berlinkeys/Berlin/EDA/ressources/acheron_3d_models/BM04B-ASRS-TF.STEP

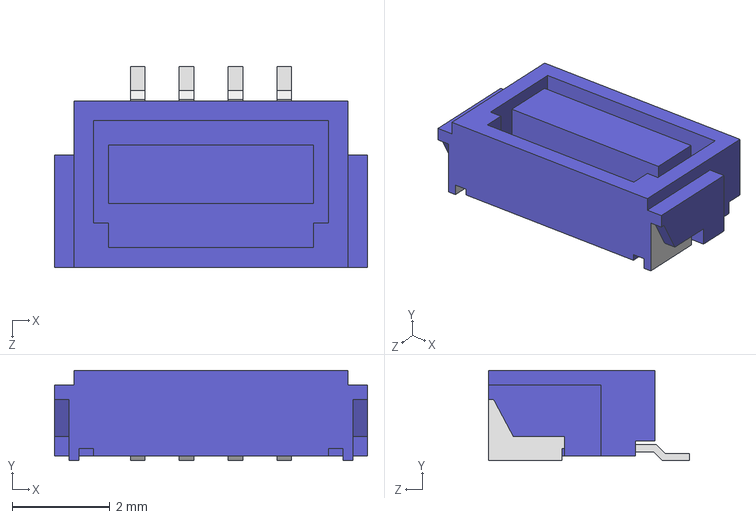
[picture p15: CAD file, 2022-06-08]
EDA/ressources/acheron_3d_models/BM04B-ASRS-TF.STEP
6.40 x 1.85 x 4.10 mm
