berlinkeys/Berlin/EDA/ressources/acheron_3d_models/XM7D-0512.STEP

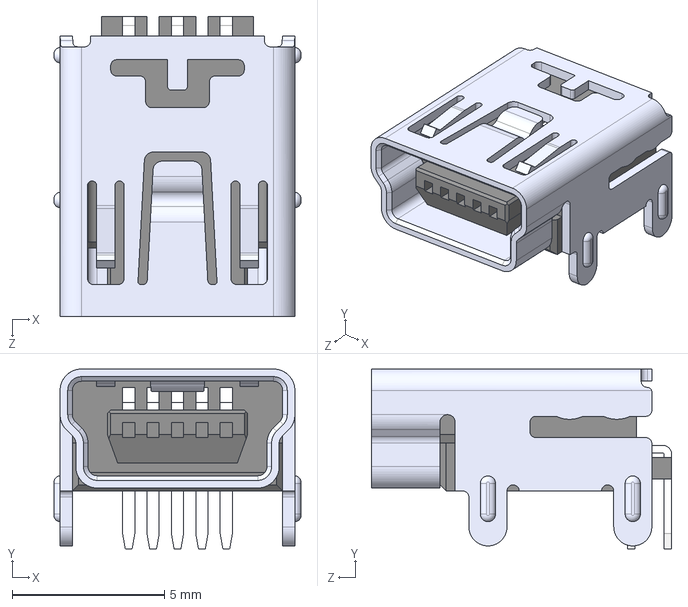
[picture p16: CAD file, 2022-06-08]
EDA/ressources/acheron_3d_models/XM7D-0512.STEP
8.10 x 5.90 x 9.85 mm
