berlinkeys/Berlin/EDA/ressources/acheron_3d_models/MDBT40.step

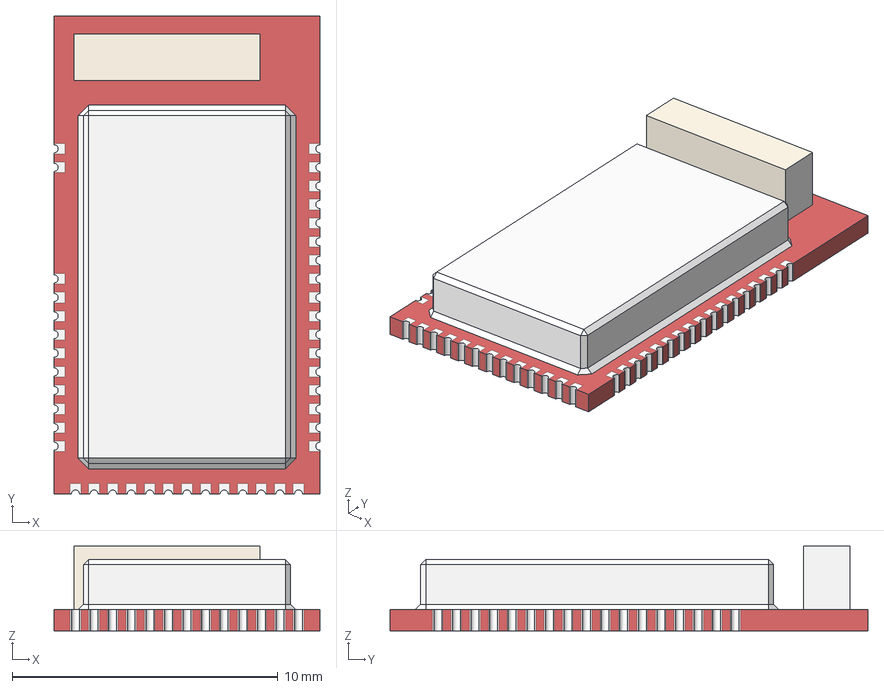
[picture p17: CAD file, 2022-06-08]
EDA/ressources/acheron_3d_models/MDBT40.step
10.0 x 18.0 x 3.20 mm
