berlinkeys/Berlin/EDA/ressources/acheron_3d_models/5032_XTAL.step

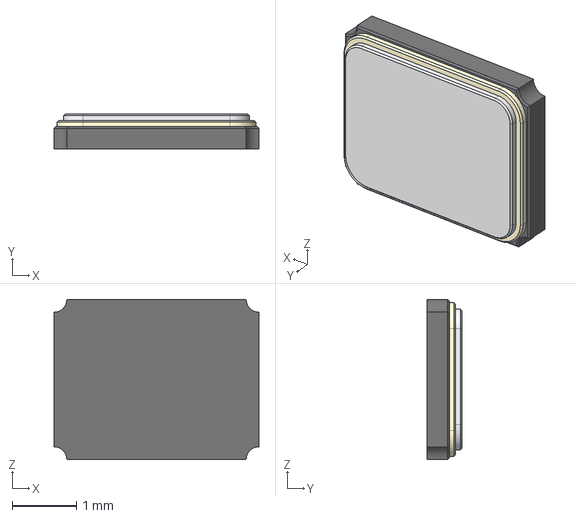
[picture p18: CAD file, 2022-06-08]
EDA/ressources/acheron_3d_models/5032_XTAL.step
3.20 x 0.55 x 2.50 mm
