berlinkeys/Berlin/EDA/ressources/acheron_3d_models/6028SMDRGB.iges

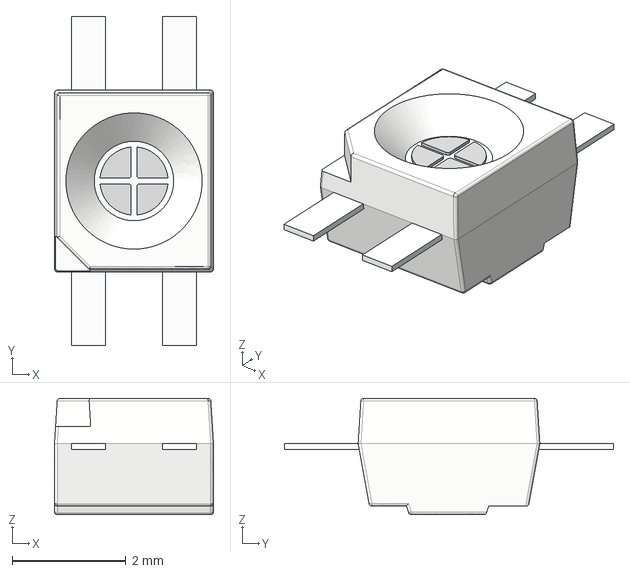
[picture p19: CAD file, 2022-06-08]
EDA/ressources/acheron_3d_models/6028SMDRGB.iges
2.80 x 5.80 x 2.05 mm
