berlinkeys/Berlin/EDA/ressources/acheron_3d_models/angle4PinHeader.step

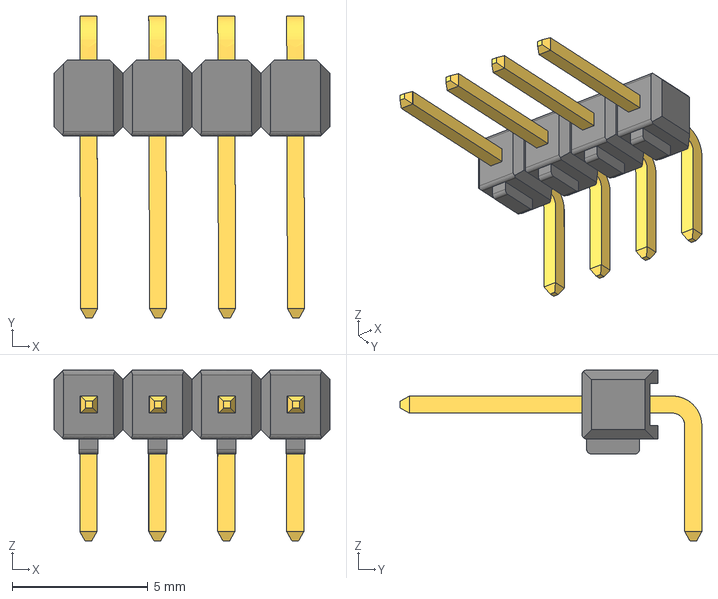
[picture p20: CAD file, 2022-06-08]
EDA/ressources/acheron_3d_models/angle4PinHeader.step
10.2 x 11.1 x 6.29 mm
