berlinkeys/Berlin/EDA/ressources/acheron_3d_models/E6C1209RGB.iges

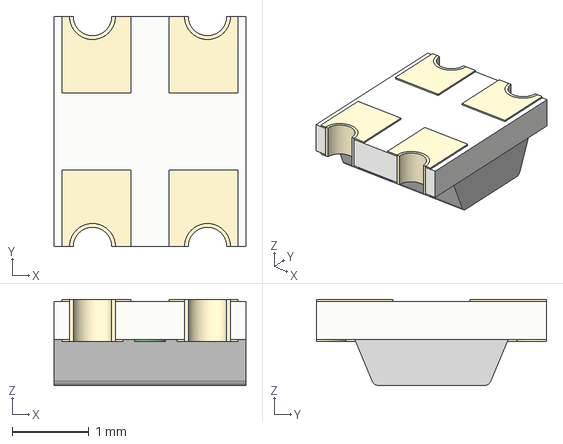
[picture p21: CAD file, 2022-06-08]
EDA/ressources/acheron_3d_models/E6C1209RGB.iges
2.50 x 3.00 x 1.12 mm
