berlinkeys/Berlin/EDA/ressources/acheron_3d_models/TE-2132415-4.stp

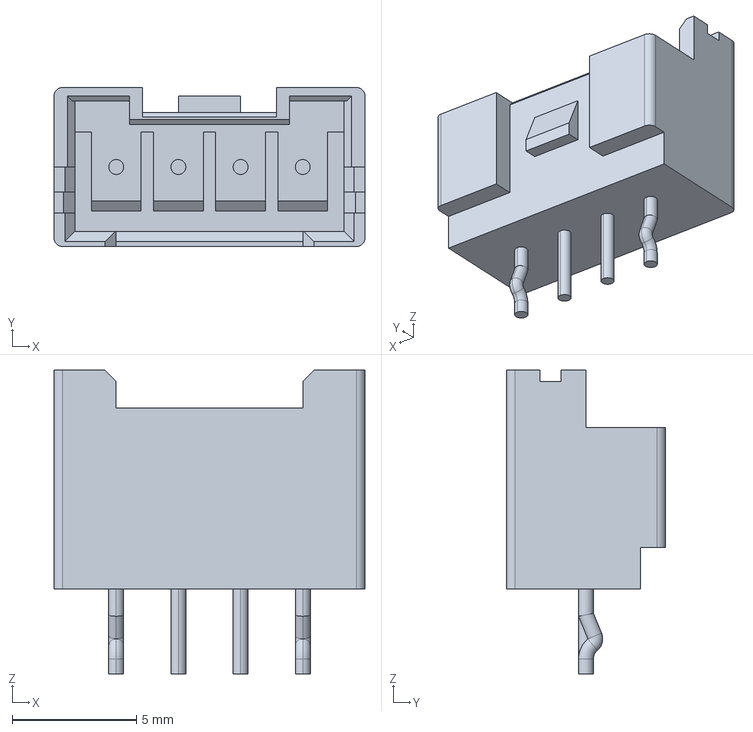
[picture p22: CAD file, 2022-06-08]
EDA/ressources/acheron_3d_models/TE-2132415-4.stp
12.5 x 6.40 x 12.2 mm
