berlinkeys/Berlin/EDA/ressources/acheron_3d_models/WS2812.stp

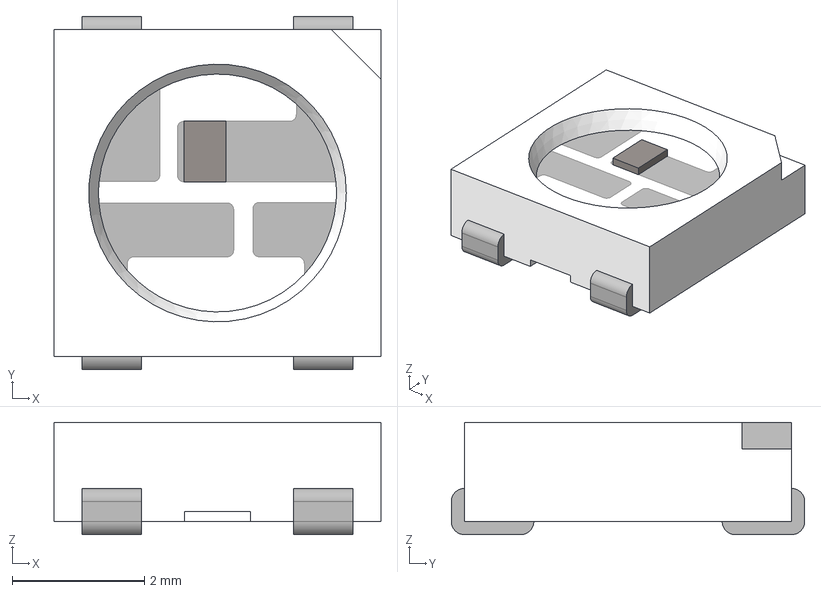
[picture p23: CAD file, 2022-06-08]
EDA/ressources/acheron_3d_models/WS2812.stp
4.95 x 5.35 x 1.70 mm
