berlinkeys/Berlin/EDA/ressources/acheron_3d_models/ALPS_EC11E.stp

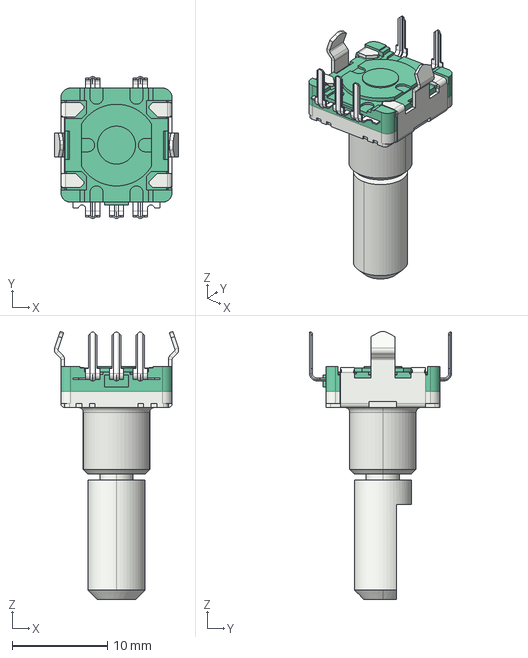
[picture p24: CAD file, 2022-06-08]
EDA/ressources/acheron_3d_models/ALPS_EC11E.stp
13.1 x 15.0 x 28.2 mm
