berlinkeys/Berlin/EDA/ressources/acheron_3d_models/BM04B-SRSS.step

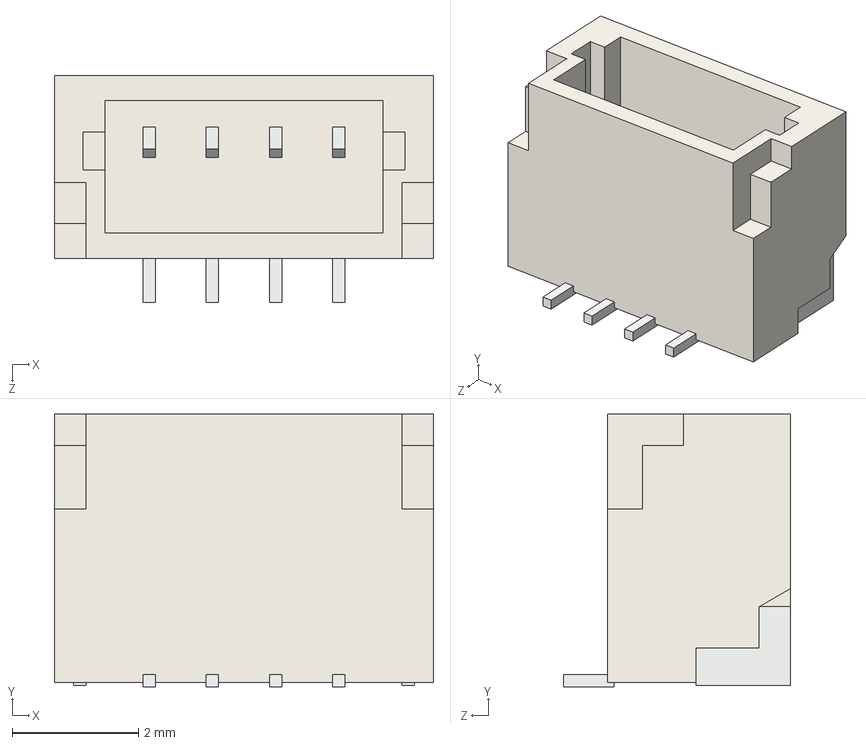
[picture p25: CAD file, 2022-06-08]
EDA/ressources/acheron_3d_models/BM04B-SRSS.step
6.00 x 4.32 x 3.60 mm
