berlinkeys/Berlin/EDA/ressources/acheron_3d_models/TYPE-C-31-M-12.step

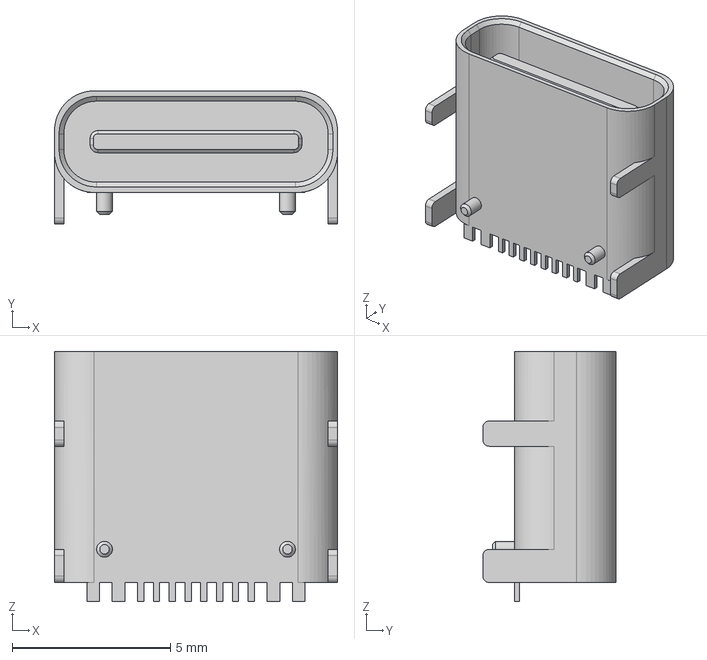
[picture p26: CAD file, 2022-06-08]
EDA/ressources/acheron_3d_models/TYPE-C-31-M-12.step
8.94 x 4.21 x 7.90 mm
