berlinkeys/Berlin/EDA/ressources/acheron_3d_models/ACM2012-2P.STEP

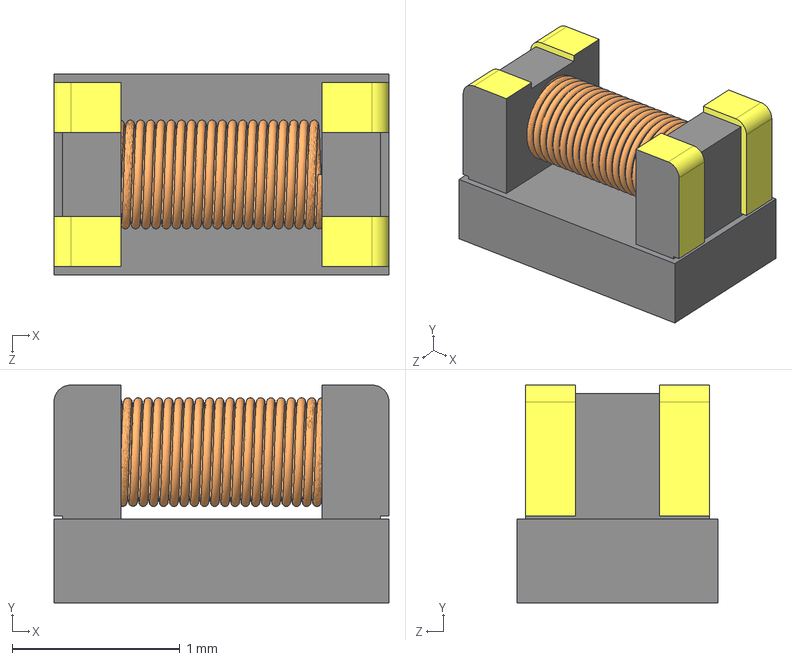
[picture p27: CAD file, 2022-06-08]
EDA/ressources/acheron_3d_models/ACM2012-2P.STEP
2.00 x 1.30 x 1.20 mm
