berlinkeys/Berlin/EDA/ressources/acheron_3d_models/RKJXT1F42001.step

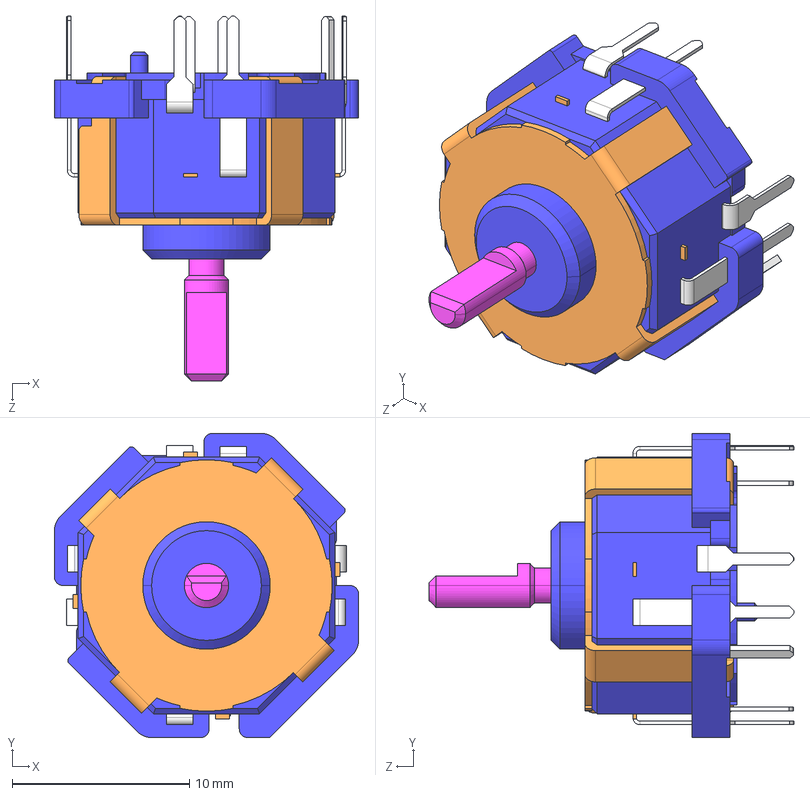
[picture p28: CAD file, 2022-06-08]
EDA/ressources/acheron_3d_models/RKJXT1F42001.step
17.2 x 17.2 x 20.6 mm
