berlinkeys/Berlin/EDA/ressources/acheron_3d_models/UX60SC-MB-5S8.stp

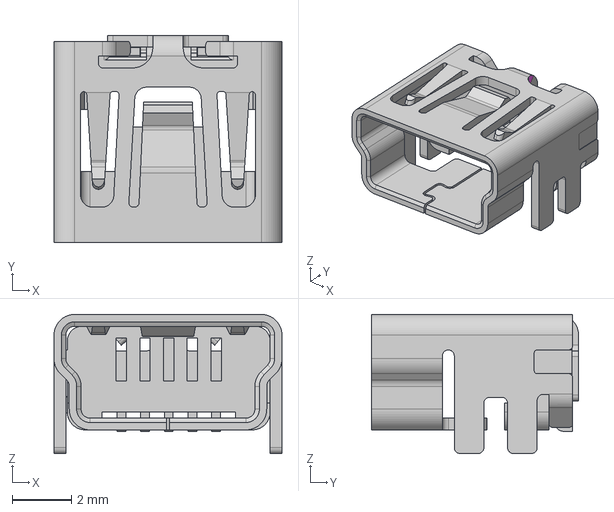
[picture p29: CAD file, 2022-06-08]
EDA/ressources/acheron_3d_models/UX60SC-MB-5S8.stp
7.70 x 7.00 x 4.70 mm
