berlinkeys/Berlin/EDA/ressources/acheron_3d_models/TYPE-C-31-M-14.step

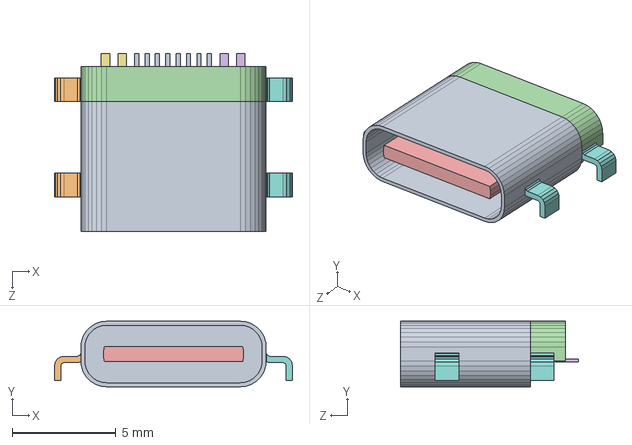
[picture p30: CAD file, 2022-06-08]
EDA/ressources/acheron_3d_models/TYPE-C-31-M-14.step
11.5 x 3.16 x 8.58 mm
