berlinkeys/Berlin/EDA/ressources/acheron_3d_models/keystone-PN3030TR.STEP

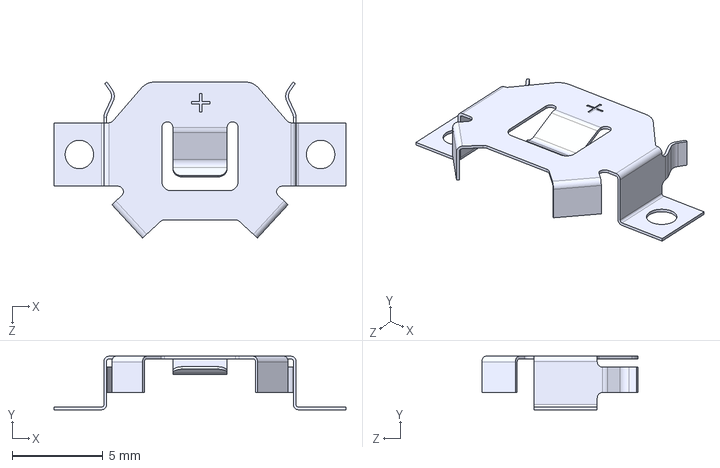
[picture p32: CAD file, 2022-06-08]
EDA/ressources/acheron_3d_models/keystone-PN3030TR.STEP
16.1 x 2.95 x 8.61 mm
