berlinkeys/Berlin/EDA/ressources/acheron_3d_models/male6PinHeader.stp

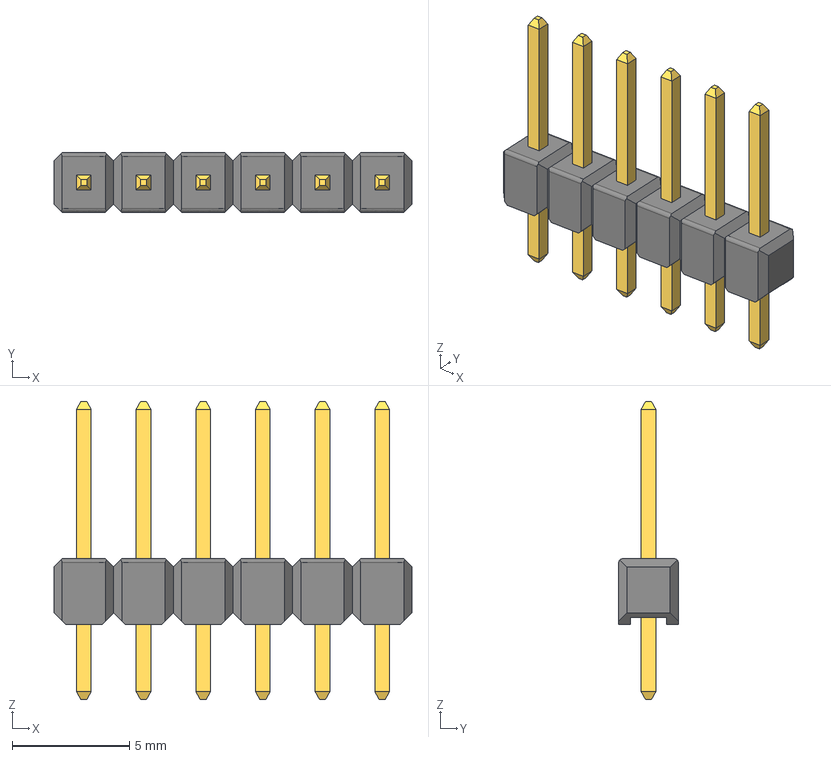
[picture p33: CAD file, 2022-06-08]
EDA/ressources/acheron_3d_models/male6PinHeader.stp
15.2 x 2.54 x 12.7 mm
