berlinkeys/Berlin/EDA/ressources/acheron_3d_models/SM20B-SRSS-TB.STEP

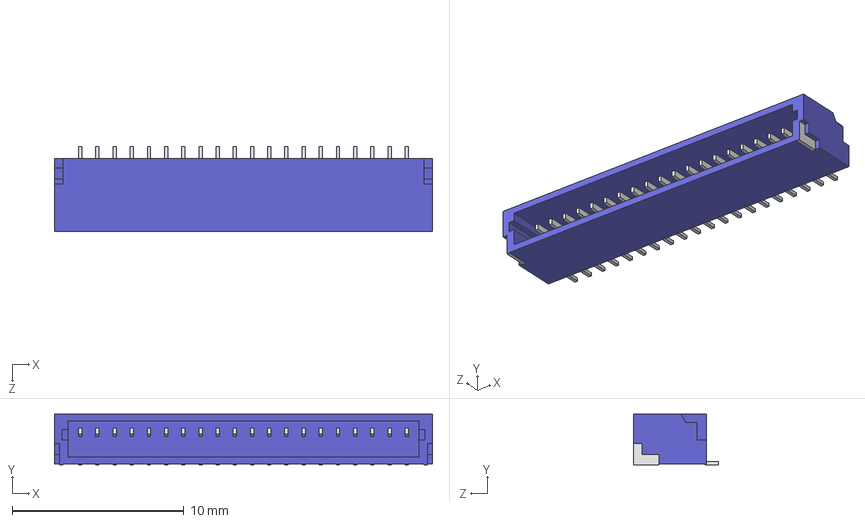
[picture p34: CAD file, 2022-06-08]
EDA/ressources/acheron_3d_models/SM20B-SRSS-TB.STEP
22.0 x 2.96 x 4.95 mm
