berlinkeys/Berlin/EDA/ressources/acheron_3d_models/Tactile_SMD_PushBtn_5x5mm.STEP

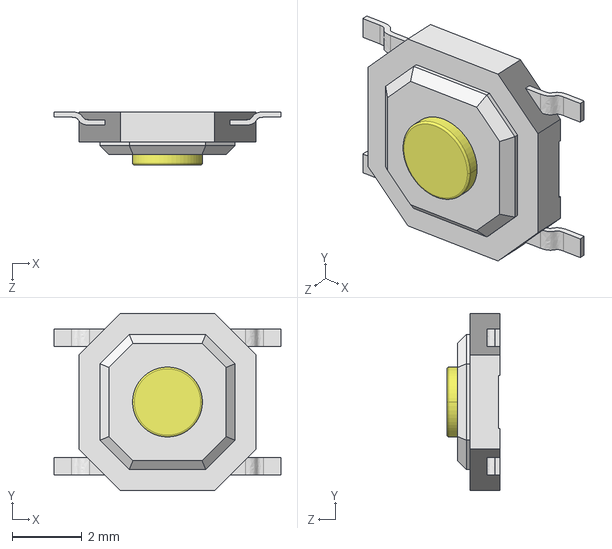
[picture p35: CAD file, 2022-06-08]
EDA/ressources/acheron_3d_models/Tactile_SMD_PushBtn_5x5mm.STEP
6.50 x 5.08 x 1.52 mm
