berlinkeys/Berlin/EDA/ressources/acheron_3d_models/kailh_socket_mx.stp

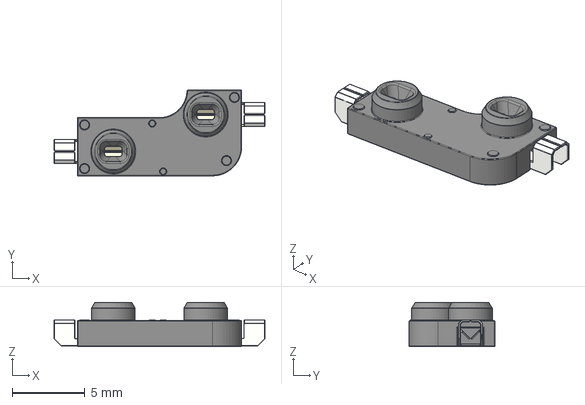
[picture p36: CAD file, 2022-06-08]
EDA/ressources/acheron_3d_models/kailh_socket_mx.stp
14.5 x 5.89 x 3.05 mm
