berlinkeys/Berlin/EDA/ressources/acheron_3d_models/SM04B-SRSS-TB.STEP

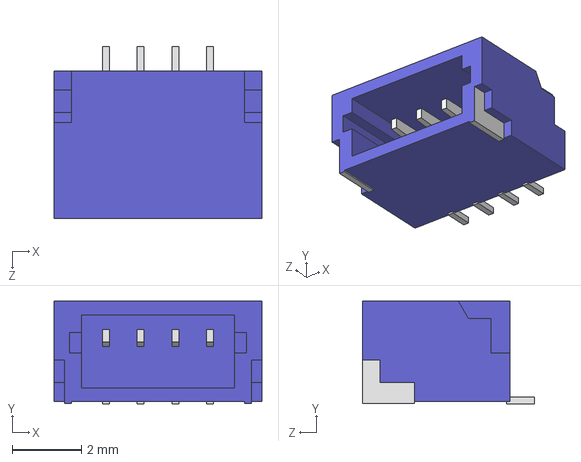
[picture p37: CAD file, 2022-06-08]
EDA/ressources/acheron_3d_models/SM04B-SRSS-TB.STEP
6.00 x 2.96 x 4.95 mm
