berlinkeys/Berlin/EDA/ressources/acheron_3d_models/3313J-1-202E.stp

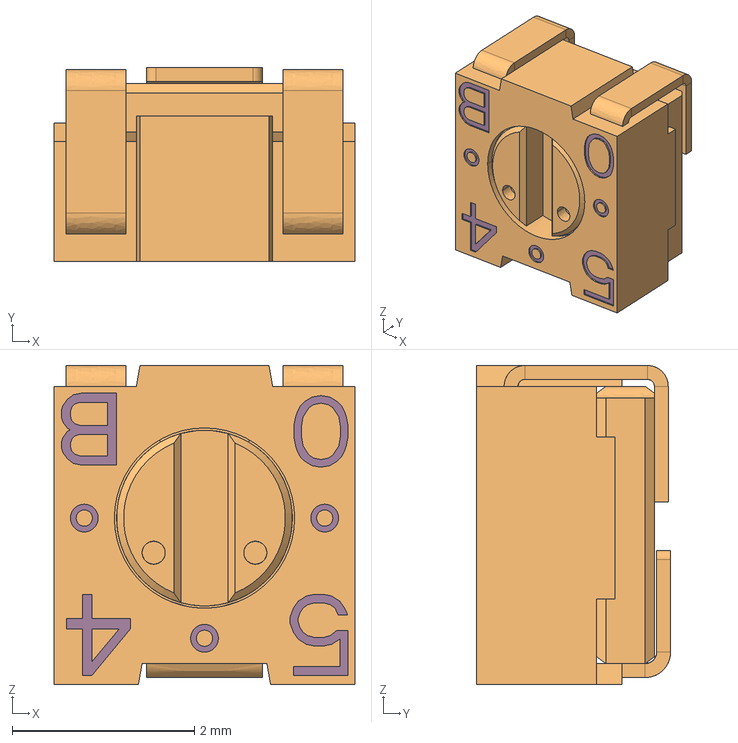
[picture p38: CAD file, 2022-06-08]
EDA/ressources/acheron_3d_models/3313J-1-202E.stp
3.30 x 2.13 x 3.51 mm
