berlinkeys/Berlin/EDA/ressources/acheron_3d_models/4PinHeader.step

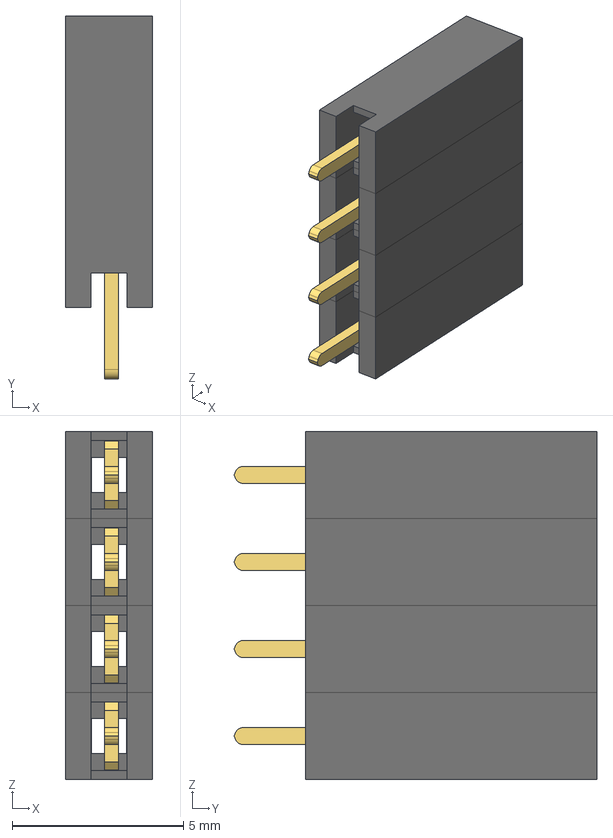
[picture p39: CAD file, 2022-06-08]
EDA/ressources/acheron_3d_models/4PinHeader.step
2.54 x 10.6 x 10.2 mm
header-1 x 4
pin-1 x 4
