berlinkeys/Berlin/EDA/ressources/acheron_3d_models/mx_switch.step

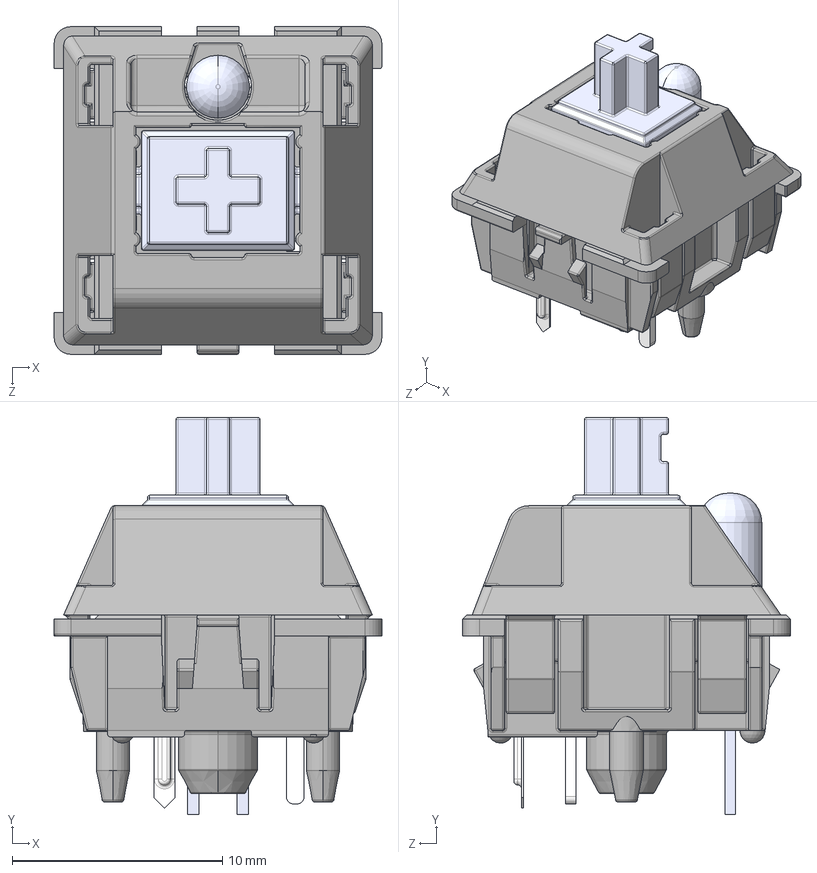
[picture p40: CAD file, 2022-06-08]
EDA/ressources/acheron_3d_models/mx_switch.step
15.6 x 18.9 x 15.6 mm
MX 轴 按键′_ü___¨1
MX 轴 轴体áì_¨￠¨__
MX粣 拸簽LEDLEDLED
MX轴 轴体 底部 μ×2__默认_á2____è_
针脚___默认__è_
