berlinkeys/Berlin/EDA/snapshot_0.7/berlin.kicad_sch

## KiCad design EDA/snapshot_0.7/berlin.kicad_sch (2023-06-23, an earlier design)

Schematic: berlin.kicad_sch

Parts:
C101, C102: 100n; C_1206_3216Metric_Pad1.42x1.75mm_HandSolder
C701, C704, C705, C717: 22uF; C_1206_3216Metric_Pad1.42x1.75mm_HandSolder
C703, C707, C708, C709, C710: 100n; C_0805_2012Metric_Pad1.15x1.40mm_HandSolder
C706, C715: 10u; C_1206_3216Metric_Pad1.42x1.75mm_HandSolder
C711: 100nF; C_0805_2012Metric_Pad1.15x1.40mm_HandSolder
C714: 4.7n; C_0805_2012Metric_Pad1.15x1.40mm_HandSolder
D2, D3, D4, D5, D6, D7, D8, D9, D10, D11, D12, D13, D14, D15, D16, D17, D18, D19, D20, D21, D22, D23, D24, D25, D26, D27, D28, D29, D30, D31, D32, D33, D34, D35, D36, D37, D38, D39, D40, D41, D42, D43, D44, D45, D46, D47, D48, D49, D50, D51, D52, D53, D54, D55, D56, D57, D58, D59, D60, D61, D62, D63, D64, D65, D66, D67, D68, D69, D70, D71, D72, D73, D74, D75, D76, D77, D78, D79, D80, D81, D82, D83, D84, D85, D86, D87, D88, D89, D90, D91, D92, D93, D94, D95, D96, D97, D98, D99, D100, D101, D103, D104, D105, D106, D107, D108, D109, D110, D111, D112, D113, D114, D115, D116, D117, D118, D119, D120, D121, D122, D123, D124, D703: 1N4148; D_SOD-123
D701: RB060M-60TR; D_SOD-123
F701: 1.5A Polyfuse; Fuse_1812_4532Metric_Pad1.30x3.40mm_HandSolder
J201: TYPE-C-31-M12_13; TYPE-C-31-M-12
J202: Conn_ARM_JTAG_SWD_10; PinSocket_2x05_P2.54mm_Vertical
J203: LCDCON
L1, L2, L702: L_Core_Ferrite; L_0805_2012Metric_Pad1.15x1.40mm_HandSolder
L701: 6.8uH; Sumida0624CDMCC
LED1,1, LED1,16: WS2811S; MSOP8_WDS
LED1,2, LED1,3, LED1,4, LED1,5, LED1,6, LED1,7, LED1,8, LED1,9, LED1,10, LED1,11, LED1,12, LED1,13, LED1,14, LED1,15, LED2,1, LED2,2, LED2,3, LED2,4, LED2,5, LED2,6, LED2,7, LED2,8, LED2,9, LED2,10, LED2,11, LED2,12, LED2,13, LED2,14, LED2,15, LED2,16, LED2,17, LED2,18, LED2,19, LED3,1, LED3,2, LED3,3, LED3,4, LED3,5, LED3,6, LED3,7, LED3,8, LED3,9, LED3,10, LED3,11, LED3,12, LED3,13, LED3,14, LED3,15, LED3,16, LED3,17, LED3,18, LED3,19, LED4,1, LED4,2, LED4,3, LED4,4, LED4,5, LED4,6, LED4,7, LED4,8, LED4,9, LED4,10, LED4,11, LED4,12, LED4,13, LED4,14, LED4,15, LED4,16, LED4,17, LED4,18, LED4,19, LED5,1, LED5,2, LED5,3, LED5,4, LED5,5, LED5,6, LED5,7, LED5,8, LED5,9, LED5,10, LED5,11, LED5,12, LED5,13, LED5,14, LED5,15, LED5,16, LED5,17, LED5,18, LED5,19, LED6,1, LED6,2, LED6,3, LED6,4, LED6,5, LED6,6, LED6,7, LED6,8, LED6,9, LED6,10, LED6,11, LED6,12, LED6,13, LED6,15, LED6,17, LED6,18, LED6,19, LED7,1, LED7,2, LED7,3, LED7,5, LED7,6, LED7,7, LED7,8, LED7,9, LED7,10, LED7,11, LED7,12, LED7,13, LED7,14, LED7,15, LED7,16, LED7,17, LED7,18: SK6812MINI-E; SK6812MINI_3535_6028_3.2x2.8mm_Round; MPN SK812MINI-E
Q701: DTC123J; SOT-23
R101, R102: 33; R_0805_2012Metric_Pad1.15x1.40mm_HandSolder
R701: 100k; R_0805_2012Metric_Pad1.15x1.40mm_HandSolder
R702: 1M 1%; R_0805_2012Metric_Pad1.15x1.40mm_HandSolder
R703: 100 1%; R_0805_2012Metric_Pad1.15x1.40mm_HandSolder
R705, R706: 5.1k; R_0805_2012Metric_Pad1.15x1.40mm_HandSolder
R711: 330k 1%; R_0805_2012Metric_Pad1.15x1.40mm_HandSolder
RV204, RV205, RV206: R_Potentiometer_MountingPin
SW1,1, SW1,16: Rotary_Encoder_Switch_Chassis; ALPS_EC11E
SW1,2, SW1,3, SW1,4, SW1,5, SW1,6, SW1,7, SW1,8, SW1,9, SW1,10, SW1,11, SW1,12, SW1,13, SW1,14, SW1,15, SW2,1, SW2,2, SW2,3, SW2,4, SW2,5, SW2,6, SW2,7, SW2,9, SW2,10, SW2,11, SW2,12, SW2,13, SW2,14, SW2,15, SW2,16, SW2,17, SW3,1, SW3,2, SW3,3, SW3,4, SW3,5, SW3,6, SW3,7, SW3,8, SW3,9, SW3,10, SW3,11, SW3,12, SW3,13, SW3,14, SW3,15, SW3,16, SW3,17, SW3,18, SW3,19, SW4,2, SW4,3, SW4,4, SW4,5, SW4,6, SW4,7, SW4,8, SW4,9, SW4,10, SW4,11, SW4,12, SW4,13, SW4,14, SW4,15, SW4,16, SW4,17, SW4,18, SW4,19, SW5,2, SW5,3, SW5,4, SW5,5, SW5,6, SW5,7, SW5,8, SW5,9, SW5,10, SW5,11, SW5,12, SW5,13, SW5,14, SW5,15, SW5,16, SW5,17, SW5,18, SW5,19, SW6,2, SW6,3, SW6,4, SW6,5, SW6,6, SW6,7, SW6,8, SW6,9, SW6,10, SW6,11, SW6,12, SW6,15, SW6,17, SW6,18, SW6,19, SW7,8, SW7,10, SW7,11, SW7,12, SW7,14, SW7,15, SW7,16, SW7,18: MXSwitch; MX100
SW2,18, SW7,17: MXSwitch; MX200
SW2,19: MXSwitch; MX200R
SW4,1, SW7,9: MXSwitch; MX150
SW5,1, SW6,1, SW7,1, SW7,2, SW7,3: MXSwitch; MX125
SW6,13: MXSwitch; MX_ISOEnter
SW7,6: MXSwitch; MX625
SW7,13: MXSwitch; MX175
SW201: SW_Push; SW_PUSH_6mm_H5mm
U501: STM32F072VBTx; LQFP-100_14x14mm_P0.5mm
U701: USBLC6-2SC6; SOT-23-6
U702: AP63203WU-7; TSOT-23-6_HandSoldering

Connections:
1,1 B: LED1,1.3 (OUTB), SW1,1.4 (B)
1,1 G: LED1,1.2 (OUTG), SW1,1.2 (G)
1,1 INTERRUPT: SW1,1.3 (SW), SW1,16.3 (SW)
1,1 R: LED1,1.1 (OUTR), SW1,1.1 (R)
1,16 B: LED1,16.3 (OUTB), SW1,16.4 (B)
1,16 G: LED1,16.2 (OUTG), SW1,16.2 (G)
1,16 R: LED1,16.1 (OUTR), SW1,16.1 (R)
+3.3V: C704.1, C705.1, C706.1, C707.1, C708.1, C709.1, C710.1, C717.1, J202.1 (VCC), L701.2, SW201.1, U501.6 (VBAT), U501.21 (VDDA), U501.28 (VDD), U501.50 (VDD), U501.75 (VDDIO2), U501.100 (VDD), U702.1 (FB)
+5V: C701.1, D701.1 (K), F701.1, LED1,2.1 (VDD), LED1,3.1 (VDD), LED1,4.1 (VDD), LED1,5.1 (VDD), LED1,6.1 (VDD), LED1,7.1 (VDD), LED1,8.1 (VDD), LED1,9.1 (VDD), LED1,10.1 (VDD), LED1,11.1 (VDD), LED1,12.1 (VDD), LED1,13.1 (VDD), LED1,14.1 (VDD), LED1,15.1 (VDD), LED2,1.1 (VDD), LED2,2.1 (VDD), LED2,3.1 (VDD), LED2,4.1 (VDD), LED2,5.1 (VDD), LED2,6.1 (VDD), LED2,7.1 (VDD), LED2,8.1 (VDD), LED2,9.1 (VDD), LED2,10.1 (VDD), LED2,11.1 (VDD), LED2,12.1 (VDD), LED2,13.1 (VDD), LED2,14.1 (VDD), LED2,15.1 (VDD), LED2,16.1 (VDD), LED2,17.1 (VDD), LED2,18.1 (VDD), LED2,19.1 (VDD), LED3,1.1 (VDD), LED3,2.1 (VDD), LED3,3.1 (VDD), LED3,4.1 (VDD), LED3,5.1 (VDD), LED3,6.1 (VDD), LED3,7.1 (VDD), LED3,8.1 (VDD), LED3,9.1 (VDD), LED3,10.1 (VDD), LED3,11.1 (VDD), LED3,12.1 (VDD), LED3,13.1 (VDD), LED3,14.1 (VDD), LED3,15.1 (VDD), LED3,16.1 (VDD), LED3,17.1 (VDD), LED3,18.1 (VDD), LED3,19.1 (VDD), LED4,1.1 (VDD), LED4,2.1 (VDD), LED4,3.1 (VDD), LED4,4.1 (VDD), LED4,5.1 (VDD), LED4,6.1 (VDD), LED4,7.1 (VDD), LED4,8.1 (VDD), LED4,9.1 (VDD), LED4,10.1 (VDD), LED4,11.1 (VDD), LED4,12.1 (VDD), LED4,13.1 (VDD), LED4,14.1 (VDD), LED4,15.1 (VDD), LED4,16.1 (VDD), LED4,17.1 (VDD), LED4,18.1 (VDD), LED4,19.1 (VDD), R701.2, U702.2 (ENABLE), U702.3 (VIN)
BOOT0: C715.1, R702.2, R711.1, U501.94 (BOOT0)
Col1: SW2,1.1 (Col), SW3,1.1 (Col), SW4,1.1 (Col), SW5,1.1 (Col), SW6,1.1 (Col), SW7,1.1 (Col), U501.65 (PC8)
Col2: SW1,2.1 (Col), SW2,2.1 (Col), SW3,2.1 (Col), SW4,2.1 (Col), SW5,2.1 (Col), SW6,2.1 (Col), SW7,2.1 (Col), U501.66 (PC9)
Col3: SW1,3.1 (Col), SW2,3.1 (Col), SW3,3.1 (Col), SW4,3.1 (Col), SW5,3.1 (Col), SW6,3.1 (Col), SW7,3.1 (Col), U501.67 (PA8)
Col4: SW1,4.1 (Col), SW2,4.1 (Col), SW3,4.1 (Col), SW4,4.1 (Col), SW5,4.1 (Col), SW6,4.1 (Col), U501.68 (PA9)
Col5: SW1,5.1 (Col), SW2,5.1 (Col), SW3,5.1 (Col), SW4,5.1 (Col), SW5,5.1 (Col), SW6,5.1 (Col), U501.69 (PA10)
Col6: SW1,6.1 (Col), SW2,6.1 (Col), SW3,6.1 (Col), SW4,6.1 (Col), SW5,6.1 (Col), SW6,6.1 (Col), SW7,6.1 (Col), U501.64 (PC7)
Col7: SW1,7.1 (Col), SW2,7.1 (Col), SW3,7.1 (Col), SW4,7.1 (Col), SW5,7.1 (Col), SW6,7.1 (Col), U501.78 (PC10)
Col8: SW1,8.1 (Col), SW3,8.1 (Col), SW4,8.1 (Col), SW5,8.1 (Col), SW6,8.1 (Col), SW7,8.1 (Col), U501.77 (PA15)
Col9: SW1,9.1 (Col), SW2,9.1 (Col), SW3,9.1 (Col), SW4,9.1 (Col), SW5,9.1 (Col), SW6,9.1 (Col), SW7,9.1 (Col), U501.89 (PB3)
Col10: SW1,10.1 (Col), SW2,10.1 (Col), SW3,10.1 (Col), SW4,10.1 (Col), SW5,10.1 (Col), SW6,10.1 (Col), SW7,10.1 (Col), U501.51 (PB12)
Col11: SW1,11.1 (Col), SW2,11.1 (Col), SW3,11.1 (Col), SW4,11.1 (Col), SW5,11.1 (Col), SW6,11.1 (Col), SW7,11.1 (Col), U501.47 (PB10)
Col12: SW1,12.1 (Col), SW2,12.1 (Col), SW3,12.1 (Col), SW4,12.1 (Col), SW5,12.1 (Col), SW6,12.1 (Col), SW7,12.1 (Col), U501.37 (PB2)
Col13: SW1,13.1 (Col), SW2,13.1 (Col), SW3,13.1 (Col), SW4,13.1 (Col), SW5,13.1 (Col), SW6,13.1 (Col), SW7,13.1 (Col), U501.35 (PB0)
Col14: SW1,14.1 (Col), SW2,14.1 (Col), SW3,14.1 (Col), SW4,14.1 (Col), SW5,14.1 (Col), SW7,14.1 (Col), U501.34 (PC5)
Col15: SW1,15.1 (Col), SW2,15.1 (Col), SW3,15.1 (Col), SW4,15.1 (Col), SW5,15.1 (Col), SW6,15.1 (Col), SW7,15.1 (Col), U501.33 (PC4)
Col16: SW2,16.1 (Col), SW3,16.1 (Col), SW4,16.1 (Col), SW5,16.1 (Col), SW7,16.1 (Col), U501.10 (PF9)
Col17: SW2,17.1 (Col), SW3,17.1 (Col), SW4,17.1 (Col), SW5,17.1 (Col), SW6,17.1 (Col), SW7,17.1 (Col), U501.13 (PF1)
Col18: SW2,18.1 (Col), SW3,18.1 (Col), SW4,18.1 (Col), SW5,18.1 (Col), SW6,18.1 (Col), SW7,18.1 (Col), U501.12 (PF0)
Col19: SW2,19.1 (Col), SW3,19.1 (Col), SW4,19.1 (Col), SW5,19.1 (Col), SW6,19.1 (Col), U501.11 (PF10)
D+: U501.71 (PA12), U701.4 (I/O2)
D-: U501.70 (PA11), U701.6 (I/O1)
Dbus+: J201.A6 (D+), J201.B6 (D+), U701.3 (I/O2)
Dbus-: J201.A7 (D-), J201.B7 (D-), U701.1 (I/O1)
Enc1A: SW1,1.A
Enc1B: SW1,1.B
Enc2A: SW1,16.A
Enc2B: SW1,16.B
GND: C701.2, C704.2, C705.2, C706.2, C707.2, C708.2, C709.2, C710.2, C711.2, C714.2, C715.2, C717.2, D701.2 (A), J201.A1 (GND), J201.B1 (GND), J202.3 (GND), J202.5 (GND), J202.9 (GNDDetect), L2.2, L702.2, LED1,2.3 (VSS), LED1,3.3 (VSS), LED1,4.3 (VSS), LED1,5.3 (VSS), LED1,6.3 (VSS), LED1,7.3 (VSS), LED1,8.3 (VSS), LED1,9.3 (VSS), LED1,10.3 (VSS), LED1,11.3 (VSS), LED1,12.3 (VSS), LED1,13.3 (VSS), LED1,14.3 (VSS), LED1,15.3 (VSS), LED2,1.3 (VSS), LED2,2.3 (VSS), LED2,3.3 (VSS), LED2,4.3 (VSS), LED2,5.3 (VSS), LED2,6.3 (VSS), LED2,7.3 (VSS), LED2,8.3 (VSS), LED2,9.3 (VSS), LED2,10.3 (VSS), LED2,11.3 (VSS), LED2,12.3 (VSS), LED2,13.3 (VSS), LED2,14.3 (VSS), LED2,15.3 (VSS), LED2,16.3 (VSS), LED2,17.3 (VSS), LED2,18.3 (VSS), LED2,19.3 (VSS), LED3,1.3 (VSS), LED3,2.3 (VSS), LED3,3.3 (VSS), LED3,4.3 (VSS), LED3,5.3 (VSS), LED3,6.3 (VSS), LED3,7.3 (VSS), LED3,8.3 (VSS), LED3,9.3 (VSS), LED3,10.3 (VSS), LED3,11.3 (VSS), LED3,12.3 (VSS), LED3,13.3 (VSS), LED3,14.3 (VSS), LED3,15.3 (VSS), LED3,16.3 (VSS), LED3,17.3 (VSS), LED3,18.3 (VSS), LED3,19.3 (VSS), LED4,1.3 (VSS), LED4,2.3 (VSS), LED4,3.3 (VSS), LED4,4.3 (VSS), LED4,5.3 (VSS), LED4,6.3 (VSS), LED4,7.3 (VSS), LED4,8.3 (VSS), LED4,9.3 (VSS), LED4,10.3 (VSS), LED4,11.3 (VSS), LED4,12.3 (VSS), LED4,13.3 (VSS), LED4,14.3 (VSS), LED4,15.3 (VSS), LED4,16.3 (VSS), LED4,17.3 (VSS), LED4,18.3 (VSS), LED4,19.3 (VSS), Q701.2 (E), R701.1, R702.1, R705.1, R706.2, SW1,16.C, U501.20 (VSSA), U501.27 (VSS), U501.49 (VSS), U501.74 (VSS), U501.99 (VSS), U701.2 (GND), U702.4 (GND)
LCD-CLK: J203.3, U501.30 (PA5)
LCD-CS: J203.6, U501.19 (PF2)
LCD-INT: J203.7, U501.18 (PC3)
LCD-PD: J203.8, U501.17 (PC2)
LCD-SPI0: J203.5, U501.32 (PA7)
LCD-SPI1: J203.4, U501.31 (PA6)
LCD-SPI2: J203.11, U501.16 (PC1)
LCD-SPI3: J203.12, U501.15 (PC0)
LED1: LED1,1.6 (DIN)
NRST: C711.1, J202.10 (~RESET), R703.1, U501.14 (NRST)
unnamed: C101.1, LED1,1.8 (VDD), R101.2
unnamed: C102.1, LED1,16.8 (VDD), R102.2
unnamed: C703.1, U702.6 (BST)
unnamed: C703.2, L701.1, U702.5 (SW)
unnamed: D2.2 (A), SW2,1.2 (Row)
unnamed: D3.2 (A), SW3,1.2 (Row)
unnamed: D4.2 (A), SW4,1.2 (Row)
unnamed: D5.2 (A), SW5,1.2 (Row)
unnamed: D6.2 (A), SW6,1.2 (Row)
unnamed: D7.2 (A), SW7,1.2 (Row)
unnamed: D8.2 (A), SW1,2.2 (Row)
unnamed: D9.2 (A), SW2,2.2 (Row)
unnamed: D10.2 (A), SW3,2.2 (Row)
unnamed: D11.2 (A), SW4,2.2 (Row)
unnamed: D12.2 (A), SW5,2.2 (Row)
unnamed: D13.2 (A), SW6,2.2 (Row)
unnamed: D14.2 (A), SW7,2.2 (Row)
unnamed: D15.2 (A), SW1,3.2 (Row)
unnamed: D16.2 (A), SW2,3.2 (Row)
unnamed: D17.2 (A), SW3,3.2 (Row)
unnamed: D18.2 (A), SW4,3.2 (Row)
unnamed: D19.2 (A), SW5,3.2 (Row)
unnamed: D20.2 (A), SW6,3.2 (Row)
unnamed: D21.2 (A), SW7,3.2 (Row)
unnamed: D22.2 (A), SW1,4.2 (Row)
unnamed: D23.2 (A), SW2,4.2 (Row)
unnamed: D24.2 (A), SW3,4.2 (Row)
unnamed: D25.2 (A), SW4,4.2 (Row)
unnamed: D26.2 (A), SW5,4.2 (Row)
unnamed: D27.2 (A), SW6,4.2 (Row)
unnamed: D28.2 (A), SW1,5.2 (Row)
unnamed: D29.2 (A), SW2,5.2 (Row)
unnamed: D30.2 (A), SW3,5.2 (Row)
unnamed: D31.2 (A), SW4,5.2 (Row)
unnamed: D32.2 (A), SW5,5.2 (Row)
unnamed: D33.2 (A), SW6,5.2 (Row)
unnamed: D34.2 (A), SW1,6.2 (Row)
unnamed: D35.2 (A), SW2,6.2 (Row)
unnamed: D36.2 (A), SW3,6.2 (Row)
unnamed: D37.2 (A), SW4,6.2 (Row)
unnamed: D38.2 (A), SW5,6.2 (Row)
unnamed: D39.2 (A), SW6,6.2 (Row)
unnamed: D40.2 (A), SW7,6.2 (Row)
unnamed: D41.2 (A), SW1,7.2 (Row)
unnamed: D42.2 (A), SW2,7.2 (Row)
unnamed: D43.2 (A), SW3,7.2 (Row)
unnamed: D44.2 (A), SW4,7.2 (Row)
unnamed: D45.2 (A), SW5,7.2 (Row)
unnamed: D46.2 (A), SW6,7.2 (Row)
unnamed: D47.2 (A), SW1,8.2 (Row)
unnamed: D49.2 (A), SW3,8.2 (Row)
unnamed: D50.2 (A), SW4,8.2 (Row)
unnamed: D51.2 (A), SW5,8.2 (Row)
unnamed: D52.2 (A), SW6,8.2 (Row)
unnamed: D53.2 (A), SW7,8.2 (Row)
unnamed: D54.2 (A), SW1,9.2 (Row)
unnamed: D55.2 (A), SW2,9.2 (Row)
unnamed: D56.2 (A), SW3,9.2 (Row)
unnamed: D57.2 (A), SW4,9.2 (Row)
unnamed: D58.2 (A), SW5,9.2 (Row)
unnamed: D59.2 (A), SW6,9.2 (Row)
unnamed: D60.2 (A), SW7,9.2 (Row)
unnamed: D61.2 (A), SW1,10.2 (Row)
unnamed: D62.2 (A), SW2,10.2 (Row)
unnamed: D63.2 (A), SW3,10.2 (Row)
unnamed: D64.2 (A), SW4,10.2 (Row)
unnamed: D65.2 (A), SW5,10.2 (Row)
unnamed: D66.2 (A), SW6,10.2 (Row)
unnamed: D67.2 (A), SW7,10.2 (Row)
unnamed: D68.2 (A), SW1,11.2 (Row)
unnamed: D69.2 (A), SW2,11.2 (Row)
unnamed: D70.2 (A), SW3,11.2 (Row)
unnamed: D71.2 (A), SW4,11.2 (Row)
unnamed: D72.2 (A), SW5,11.2 (Row)
unnamed: D73.2 (A), SW6,11.2 (Row)
unnamed: D74.2 (A), SW7,11.2 (Row)
unnamed: D75.2 (A), SW1,12.2 (Row)
unnamed: D76.2 (A), SW2,12.2 (Row)
unnamed: D77.2 (A), SW3,12.2 (Row)
unnamed: D78.2 (A), SW4,12.2 (Row)
unnamed: D79.2 (A), SW5,12.2 (Row)
unnamed: D80.2 (A), SW6,12.2 (Row)
unnamed: D81.2 (A), SW7,12.2 (Row)
unnamed: D82.2 (A), SW1,13.2 (Row)
unnamed: D83.2 (A), SW2,13.2 (Row)
unnamed: D84.2 (A), SW3,13.2 (Row)
unnamed: D85.2 (A), SW4,13.2 (Row)
unnamed: D86.2 (A), SW5,13.2 (Row)
unnamed: D87.2 (A), SW6,13.2 (Row)
unnamed: D88.2 (A), SW7,13.2 (Row)
unnamed: D89.2 (A), SW1,14.2 (Row)
unnamed: D90.2 (A), SW2,14.2 (Row)
unnamed: D91.2 (A), SW3,14.2 (Row)
unnamed: D92.2 (A), SW4,14.2 (Row)
unnamed: D93.2 (A), SW5,14.2 (Row)
unnamed: D94.2 (A), SW7,14.2 (Row)
unnamed: D95.2 (A), SW1,15.2 (Row)
unnamed: D96.2 (A), SW2,15.2 (Row)
unnamed: D97.2 (A), SW3,15.2 (Row)
unnamed: D98.2 (A), SW4,15.2 (Row)
unnamed: D99.2 (A), SW5,15.2 (Row)
unnamed: D100.2 (A), SW6,15.2 (Row)
unnamed: D101.2 (A), SW7,15.2 (Row)
unnamed: D103.2 (A), SW2,16.2 (Row)
unnamed: D104.2 (A), SW3,16.2 (Row)
unnamed: D105.2 (A), SW4,16.2 (Row)
unnamed: D106.2 (A), SW5,16.2 (Row)
unnamed: D107.2 (A), SW7,16.2 (Row)
unnamed: D108.2 (A), SW2,17.2 (Row)
unnamed: D109.2 (A), SW3,17.2 (Row)
unnamed: D110.2 (A), SW4,17.2 (Row)
unnamed: D111.2 (A), SW5,17.2 (Row)
unnamed: D112.2 (A), SW6,17.2 (Row)
unnamed: D113.2 (A), SW7,17.2 (Row)
unnamed: D114.2 (A), SW2,18.2 (Row)
unnamed: D115.2 (A), SW3,18.2 (Row)
unnamed: D116.2 (A), SW4,18.2 (Row)
unnamed: D117.2 (A), SW5,18.2 (Row)
unnamed: D118.2 (A), SW6,18.2 (Row)
unnamed: D119.2 (A), SW7,18.2 (Row)
unnamed: D120.2 (A), SW2,19.2 (Row)
unnamed: D121.2 (A), SW3,19.2 (Row)
unnamed: D122.2 (A), SW4,19.2 (Row)
unnamed: D123.2 (A), SW5,19.2 (Row)
unnamed: D124.2 (A), SW6,19.2 (Row)
unnamed: D703.1 (K), R711.2
unnamed: D703.2 (A), Q701.1 (B), SW201.2
unnamed: J201.A5 (CC1), R705.2
unnamed: J201.B5 (CC2), R706.1
unnamed: J201.S (SHIELD), L702.1
unnamed: J203.17, J203.18
unnamed: J203.19, J203.20
unnamed: L1.1, SW1,1.S (Shield)
unnamed: L1.2, SW1,1.C
unnamed: L2.1, SW1,16.S (Shield)
unnamed: LED1,1.5 (DO), LED1,2.4 (DIN)
unnamed: LED1,2.2 (DOUT), LED1,3.4 (DIN)
unnamed: LED1,3.2 (DOUT), LED1,4.4 (DIN)
unnamed: LED1,4.2 (DOUT), LED1,5.4 (DIN)
unnamed: LED1,5.2 (DOUT), LED1,6.4 (DIN)
unnamed: LED1,6.2 (DOUT), LED1,7.4 (DIN)
unnamed: LED1,7.2 (DOUT), LED1,8.4 (DIN)
unnamed: LED1,8.2 (DOUT), LED1,9.4 (DIN)
unnamed: LED1,10.2 (DOUT), LED1,11.4 (DIN)
unnamed: LED1,9.2 (DOUT), LED1,10.4 (DIN)
unnamed: LED1,11.2 (DOUT), LED1,12.4 (DIN)
unnamed: LED1,12.2 (DOUT), LED1,13.4 (DIN)
unnamed: LED1,13.2 (DOUT), LED1,14.4 (DIN)
unnamed: LED1,14.2 (DOUT), LED1,15.4 (DIN)
unnamed: LED1,15.2 (DOUT), LED1,16.6 (DIN)
unnamed: LED1,16.5 (DO), LED2,19.4 (DIN)
unnamed: LED2,1.2 (DOUT), LED3,1.4 (DIN)
unnamed: LED2,1.4 (DIN), LED2,2.2 (DOUT)
unnamed: LED2,2.4 (DIN), LED2,3.2 (DOUT)
unnamed: LED2,3.4 (DIN), LED2,4.2 (DOUT)
unnamed: LED2,4.4 (DIN), LED2,5.2 (DOUT)
unnamed: LED2,5.4 (DIN), LED2,6.2 (DOUT)
unnamed: LED2,6.4 (DIN), LED2,7.2 (DOUT)
unnamed: LED2,7.4 (DIN), LED2,8.2 (DOUT)
unnamed: LED2,8.4 (DIN), LED2,9.2 (DOUT)
unnamed: LED2,9.4 (DIN), LED2,10.2 (DOUT)
unnamed: LED2,10.4 (DIN), LED2,11.2 (DOUT)
unnamed: LED2,11.4 (DIN), LED2,12.2 (DOUT)
unnamed: LED2,12.4 (DIN), LED2,13.2 (DOUT)
unnamed: LED2,13.4 (DIN), LED2,14.2 (DOUT)
unnamed: LED2,14.4 (DIN), LED2,15.2 (DOUT)
unnamed: LED2,15.4 (DIN), LED2,16.2 (DOUT)
unnamed: LED2,16.4 (DIN), LED2,17.2 (DOUT)
unnamed: LED2,17.4 (DIN), LED2,18.2 (DOUT)
unnamed: LED2,18.4 (DIN), LED2,19.2 (DOUT)
unnamed: LED3,1.2 (DOUT), LED3,2.4 (DIN)
unnamed: LED3,2.2 (DOUT), LED3,3.4 (DIN)
unnamed: LED3,3.2 (DOUT), LED3,4.4 (DIN)
unnamed: LED3,4.2 (DOUT), LED3,5.4 (DIN)
unnamed: LED3,5.2 (DOUT), LED3,6.4 (DIN)
unnamed: LED3,6.2 (DOUT), LED3,7.4 (DIN)
unnamed: LED3,7.2 (DOUT), LED3,8.4 (DIN)
unnamed: LED3,8.2 (DOUT), LED3,9.4 (DIN)
unnamed: LED3,10.2 (DOUT), LED3,11.4 (DIN)
unnamed: LED3,9.2 (DOUT), LED3,10.4 (DIN)
unnamed: LED3,11.2 (DOUT), LED3,12.4 (DIN)
unnamed: LED3,12.2 (DOUT), LED3,13.4 (DIN)
unnamed: LED3,13.2 (DOUT), LED3,14.4 (DIN)
unnamed: LED3,14.2 (DOUT), LED3,15.4 (DIN)
unnamed: LED3,15.2 (DOUT), LED3,16.4 (DIN)
unnamed: LED3,16.2 (DOUT), LED3,17.4 (DIN)
unnamed: LED3,17.2 (DOUT), LED3,18.4 (DIN)
unnamed: LED3,18.2 (DOUT), LED3,19.4 (DIN)
unnamed: LED3,19.2 (DOUT), LED4,19.4 (DIN)
unnamed: LED4,1.2 (DOUT), LED5,1.4 (DIN)
unnamed: LED4,1.4 (DIN), LED4,2.2 (DOUT)
unnamed: LED4,2.4 (DIN), LED4,3.2 (DOUT)
unnamed: LED4,3.4 (DIN), LED4,4.2 (DOUT)
unnamed: LED4,4.4 (DIN), LED4,5.2 (DOUT)
unnamed: LED4,5.4 (DIN), LED4,6.2 (DOUT)
unnamed: LED4,6.4 (DIN), LED4,7.2 (DOUT)
unnamed: LED4,7.4 (DIN), LED4,8.2 (DOUT)
unnamed: LED4,8.4 (DIN), LED4,9.2 (DOUT)
unnamed: LED4,9.4 (DIN), LED4,10.2 (DOUT)
unnamed: LED4,10.4 (DIN), LED4,11.2 (DOUT)
unnamed: LED4,11.4 (DIN), LED4,12.2 (DOUT)
unnamed: LED4,12.4 (DIN), LED4,13.2 (DOUT)
unnamed: LED4,13.4 (DIN), LED4,14.2 (DOUT)
unnamed: LED4,14.4 (DIN), LED4,15.2 (DOUT)
unnamed: LED4,15.4 (DIN), LED4,16.2 (DOUT)
unnamed: LED4,16.4 (DIN), LED4,17.2 (DOUT)
unnamed: LED4,17.4 (DIN), LED4,18.2 (DOUT)
unnamed: LED4,18.4 (DIN), LED4,19.2 (DOUT)
unnamed: LED5,1.2 (DOUT), LED5,2.4 (DIN)
unnamed: LED5,2.2 (DOUT), LED5,3.4 (DIN)
unnamed: LED5,3.2 (DOUT), LED5,4.4 (DIN)
unnamed: LED5,4.2 (DOUT), LED5,5.4 (DIN)
unnamed: LED5,5.2 (DOUT), LED5,6.4 (DIN)
unnamed: LED5,6.2 (DOUT), LED5,7.4 (DIN)
unnamed: LED5,7.2 (DOUT), LED5,8.4 (DIN)
unnamed: LED5,8.2 (DOUT), LED5,9.4 (DIN)
unnamed: LED5,10.2 (DOUT), LED5,11.4 (DIN)
unnamed: LED5,9.2 (DOUT), LED5,10.4 (DIN)
unnamed: LED5,11.2 (DOUT), LED5,12.4 (DIN)
unnamed: LED5,12.2 (DOUT), LED5,13.4 (DIN)
unnamed: LED5,13.2 (DOUT), LED5,14.4 (DIN)
unnamed: LED5,14.2 (DOUT), LED5,15.4 (DIN)
unnamed: LED5,15.2 (DOUT), LED5,16.4 (DIN)
unnamed: LED5,16.2 (DOUT), LED5,17.4 (DIN)
unnamed: LED5,17.2 (DOUT), LED5,18.4 (DIN)
unnamed: LED5,18.2 (DOUT), LED5,19.4 (DIN)
unnamed: LED5,19.2 (DOUT), LED6,19.4 (DIN)
unnamed: LED6,1.2 (DOUT), LED7,1.4 (DIN)
unnamed: LED6,1.4 (DIN), LED6,2.2 (DOUT)
unnamed: LED6,2.4 (DIN), LED6,3.2 (DOUT)
unnamed: LED6,3.4 (DIN), LED6,4.2 (DOUT)
unnamed: LED6,4.4 (DIN), LED6,5.2 (DOUT)
unnamed: LED6,5.4 (DIN), LED6,6.2 (DOUT)
unnamed: LED6,6.4 (DIN), LED6,7.2 (DOUT)
unnamed: LED6,7.4 (DIN), LED6,8.2 (DOUT)
unnamed: LED6,8.4 (DIN), LED6,9.2 (DOUT)
unnamed: LED6,9.4 (DIN), LED6,10.2 (DOUT)
unnamed: LED6,10.4 (DIN), LED6,11.2 (DOUT)
unnamed: LED6,11.4 (DIN), LED6,12.2 (DOUT)
unnamed: LED6,12.4 (DIN), LED6,13.2 (DOUT)
unnamed: LED6,13.4 (DIN), LED6,15.2 (DOUT)
unnamed: LED6,15.4 (DIN), LED6,17.2 (DOUT)
unnamed: LED6,17.4 (DIN), LED6,18.2 (DOUT)
unnamed: LED6,18.4 (DIN), LED6,19.2 (DOUT)
unnamed: LED7,1.2 (DOUT), LED7,2.4 (DIN)
unnamed: LED7,2.2 (DOUT), LED7,3.4 (DIN)
unnamed: LED7,3.2 (DOUT), LED7,5.4 (DIN)
unnamed: LED7,5.2 (DOUT), LED7,6.4 (DIN)
unnamed: LED7,6.2 (DOUT), LED7,7.4 (DIN)
unnamed: LED7,7.2 (DOUT), LED7,8.4 (DIN)
unnamed: LED7,8.2 (DOUT), LED7,9.4 (DIN)
unnamed: LED7,10.2 (DOUT), LED7,11.4 (DIN)
unnamed: LED7,9.2 (DOUT), LED7,10.4 (DIN)
unnamed: LED7,11.2 (DOUT), LED7,12.4 (DIN)
unnamed: LED7,12.2 (DOUT), LED7,13.4 (DIN)
unnamed: LED7,13.2 (DOUT), LED7,14.4 (DIN)
unnamed: LED7,14.2 (DOUT), LED7,15.4 (DIN)
unnamed: LED7,15.2 (DOUT), LED7,16.4 (DIN)
unnamed: LED7,16.2 (DOUT), LED7,17.4 (DIN)
unnamed: LED7,17.2 (DOUT), LED7,18.4 (DIN)
unnamed: Q701.3 (C), R703.2
unnamed: RV204.1, RV204.MP (MountPin)
unnamed: RV205.1, RV205.MP (MountPin)
unnamed: RV206.1, RV206.MP (MountPin)
PV1: RV204.2
PV2: RV205.2
PV3: RV206.2
Row1: D8.1 (K), D15.1 (K), D22.1 (K), D28.1 (K), D34.1 (K), D41.1 (K), D47.1 (K), D54.1 (K), D61.1 (K), D68.1 (K), D75.1 (K), D82.1 (K), D89.1 (K), D95.1 (K), U501.90 (PB4)
Row2: D2.1 (K), D9.1 (K), D16.1 (K), D23.1 (K), D29.1 (K), D35.1 (K), D42.1 (K), D48.1 (K), D55.1 (K), D62.1 (K), D69.1 (K), D76.1 (K), D83.1 (K), D90.1 (K), D96.1 (K), D103.1 (K), D108.1 (K), D114.1 (K), D120.1 (K), U501.91 (PB5)
Row3: D3.1 (K), D10.1 (K), D17.1 (K), D24.1 (K), D30.1 (K), D36.1 (K), D43.1 (K), D49.1 (K), D56.1 (K), D63.1 (K), D70.1 (K), D77.1 (K), D84.1 (K), D91.1 (K), D97.1 (K), D104.1 (K), D109.1 (K), D115.1 (K), D121.1 (K), U501.52 (PB13)
Row4: D4.1 (K), D11.1 (K), D18.1 (K), D25.1 (K), D31.1 (K), D37.1 (K), D44.1 (K), D50.1 (K), D57.1 (K), D64.1 (K), D71.1 (K), D78.1 (K), D85.1 (K), D98.1 (K), D105.1 (K), D110.1 (K), D116.1 (K), D122.1 (K), U501.53 (PB14)
Row5: D5.1 (K), D12.1 (K), D19.1 (K), D26.1 (K), D32.1 (K), D38.1 (K), D45.1 (K), D51.1 (K), D58.1 (K), D65.1 (K), D72.1 (K), D79.1 (K), D86.1 (K), D92.1 (K), D99.1 (K), D106.1 (K), D111.1 (K), D117.1 (K), D123.1 (K), U501.54 (PB15)
Row6: D6.1 (K), D13.1 (K), D20.1 (K), D27.1 (K), D33.1 (K), D39.1 (K), D46.1 (K), D52.1 (K), D59.1 (K), D66.1 (K), D73.1 (K), D80.1 (K), D87.1 (K), D93.1 (K), D100.1 (K), D112.1 (K), D118.1 (K), D124.1 (K), U501.63 (PC6)
Row7: D7.1 (K), D14.1 (K), D21.1 (K), D40.1 (K), D53.1 (K), D60.1 (K), D67.1 (K), D74.1 (K), D81.1 (K), D88.1 (K), D94.1 (K), D101.1 (K), D107.1 (K), D113.1 (K), D119.1 (K), U501.48 (PB11)
SWCLK: J202.4 (SWDCLK/TCK), U501.76 (PA14)
SWDIO: J202.2 (SWDIO/TMS), U501.72 (PA13)
VBUS: C714.1, F701.2, J201.A4 (VBUS), J201.B4 (VBUS), U701.5 (VBUS)

Notes on the sheet:
ISO `~{}
5mm through hole LED (3D-printed version only)
PgDn
back
Backlight LEDs
RGB LED stuff
PauseBreak
ISO <> |
Logos, holes, misc.
Scroll Lock
Bypass cap for the level shifter
Down
Pots may need additional debouncing through 1. a decoupling cap between analog/3v3 2. an inductor between chassis/gnd if ADC software debounce doesn't work
SMPS provides more LED current for backlight usage.
Microprocessor Bypass caps
Ins
F10
ISO Lshift
ISP header
PrtSc
PgUp
RAlt (1.25u)
Sumida 0624CDMCCDS-6R8MC
LED PWM MOSFET
Display Header
Del
CapsLock
LAlt (1.25u)
Esc
`~{}
F11
Hole for grounding alu case
Key Matrix
Microcontroller
LCtrl (1.25u)
P11
3.3V power
Enter
Level shifter
RCtrl (1.25u)
End
ISO Enter
Bulk caps
Left
Home
Tab
SUPER (1.25u)
Right
play
P12
skip
USB
friday13
Component annotation keys: Type Shortcut+Usage Number+Part number(max. 100 parts) Usage Number: 1-Auxiliary components for matrix 2-interface components 3-auxiliary components for logic (e.g. pullups) 5-logic/ic components 7-power delivery components notes: components inside the matrix layout are a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
Menu(1.25u)
SUPER(1.25u)
USB ESD protection
pmslps4
6.25u Space
Reset circuit
F12
Lock LEDs
BackSpace
Analog Potentiometers
Holes for JLCPCB SMT tooling
NumLck
RShift
P10
