berlinkeys/Berlin/EDA/ressources/inspiration_boston06/Boston-keyboard-V06.kicad_sch

## KiCad design EDA/ressources/inspiration_boston06/Boston-keyboard-V06.kicad_sch (2022-07-23)

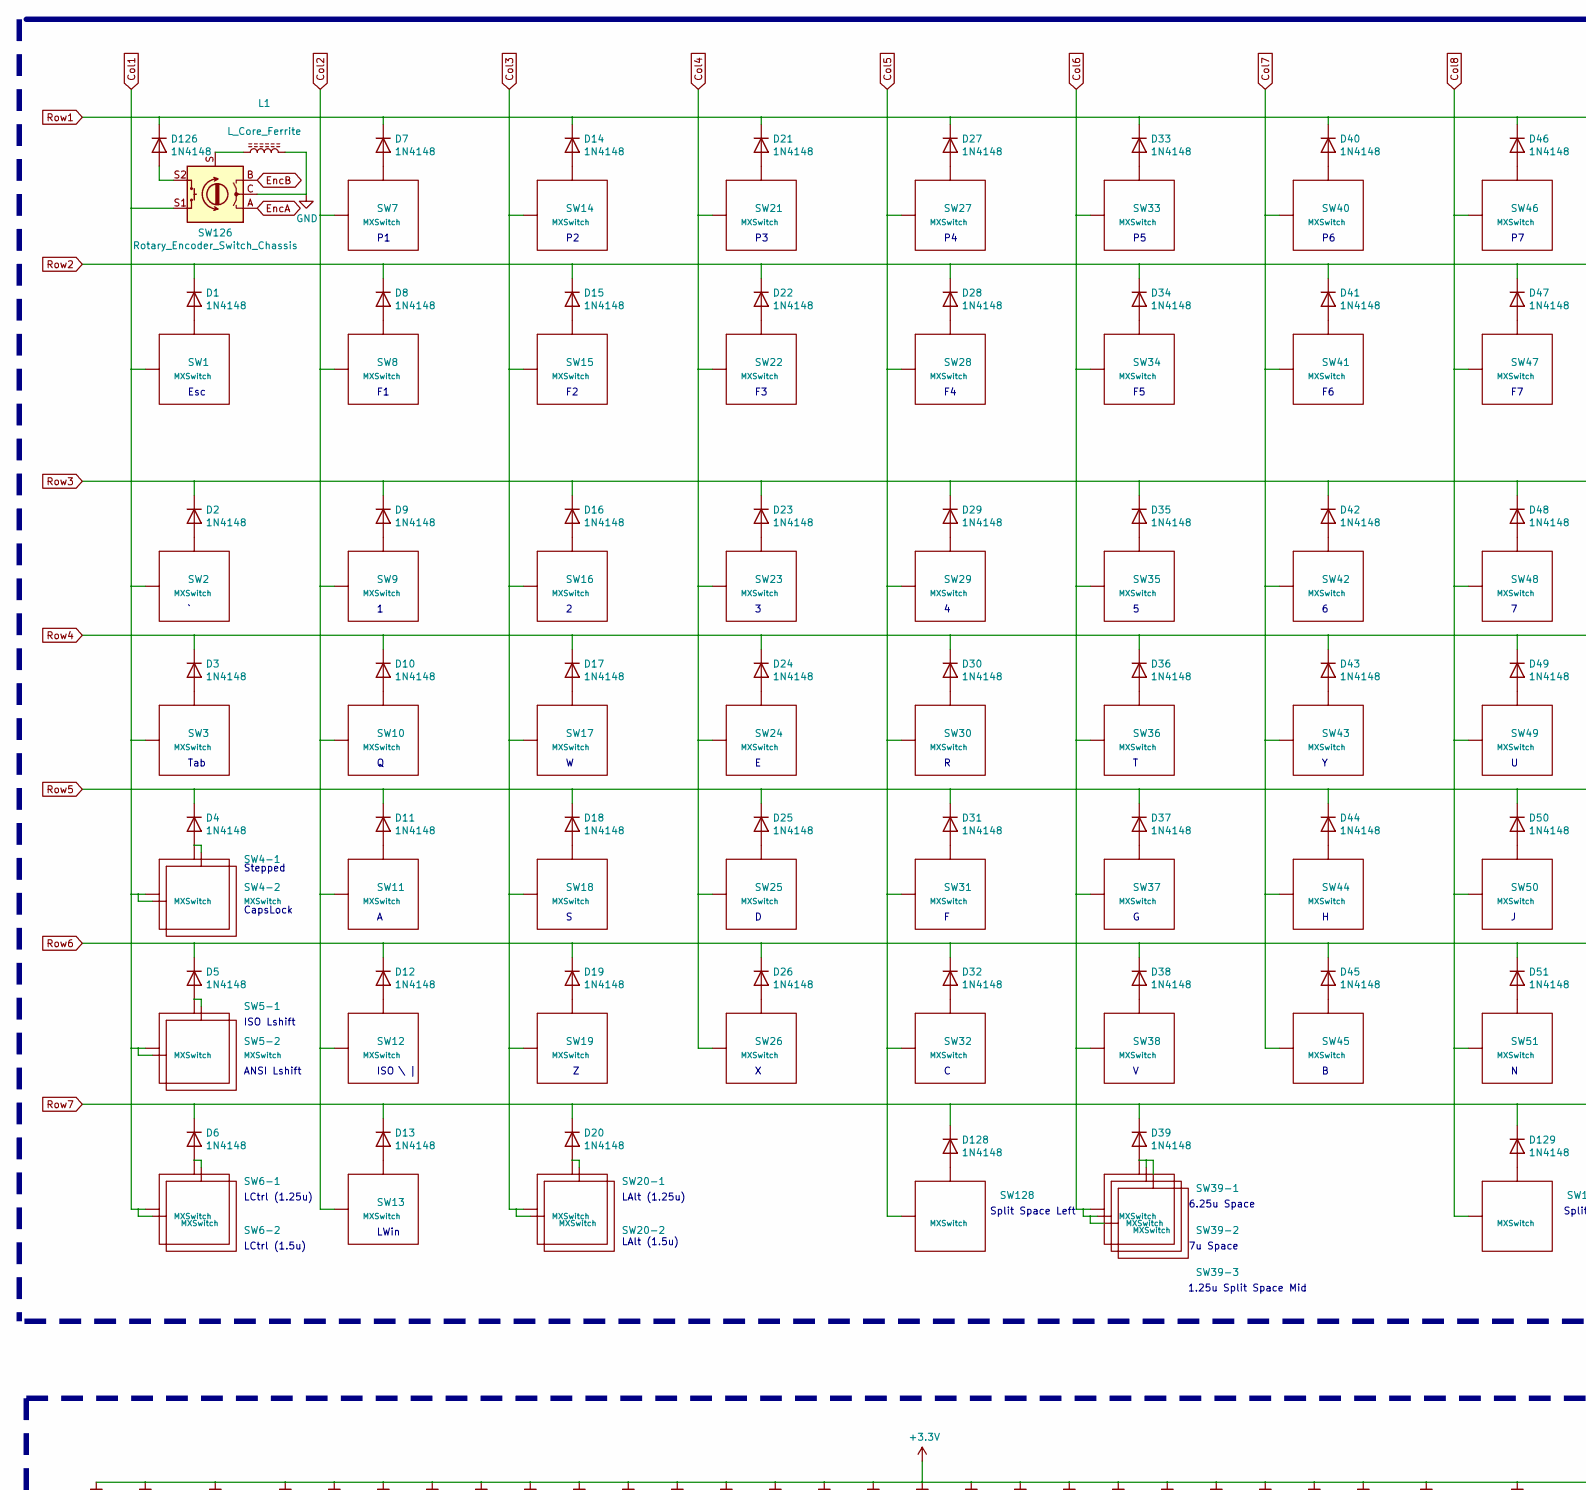
[picture p41: schematic Boston-keyboard-V06.kicad_sch, part in row 1, column 1]

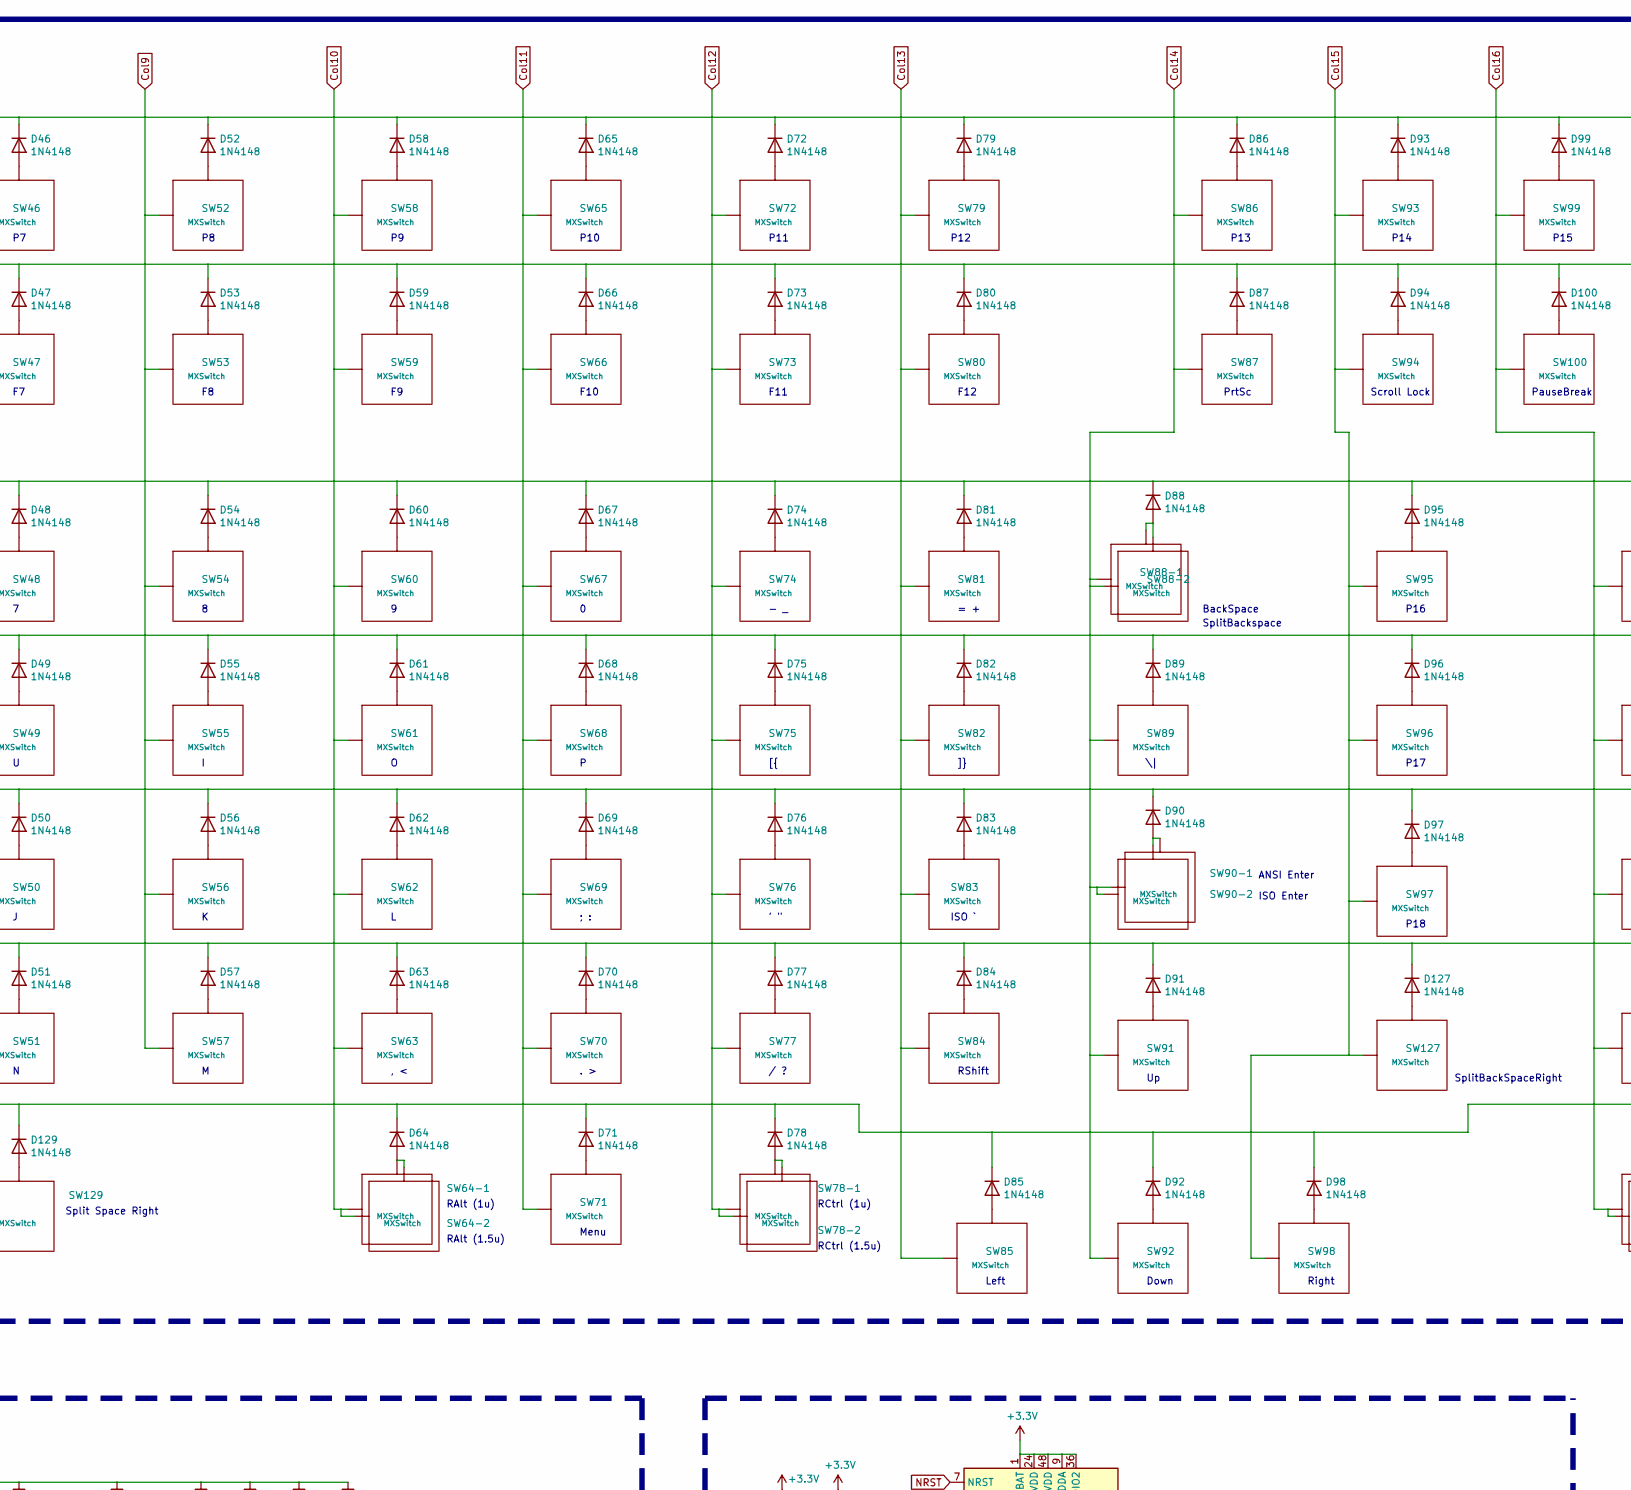
[picture p42: schematic Boston-keyboard-V06.kicad_sch, part in row 1, column 2]

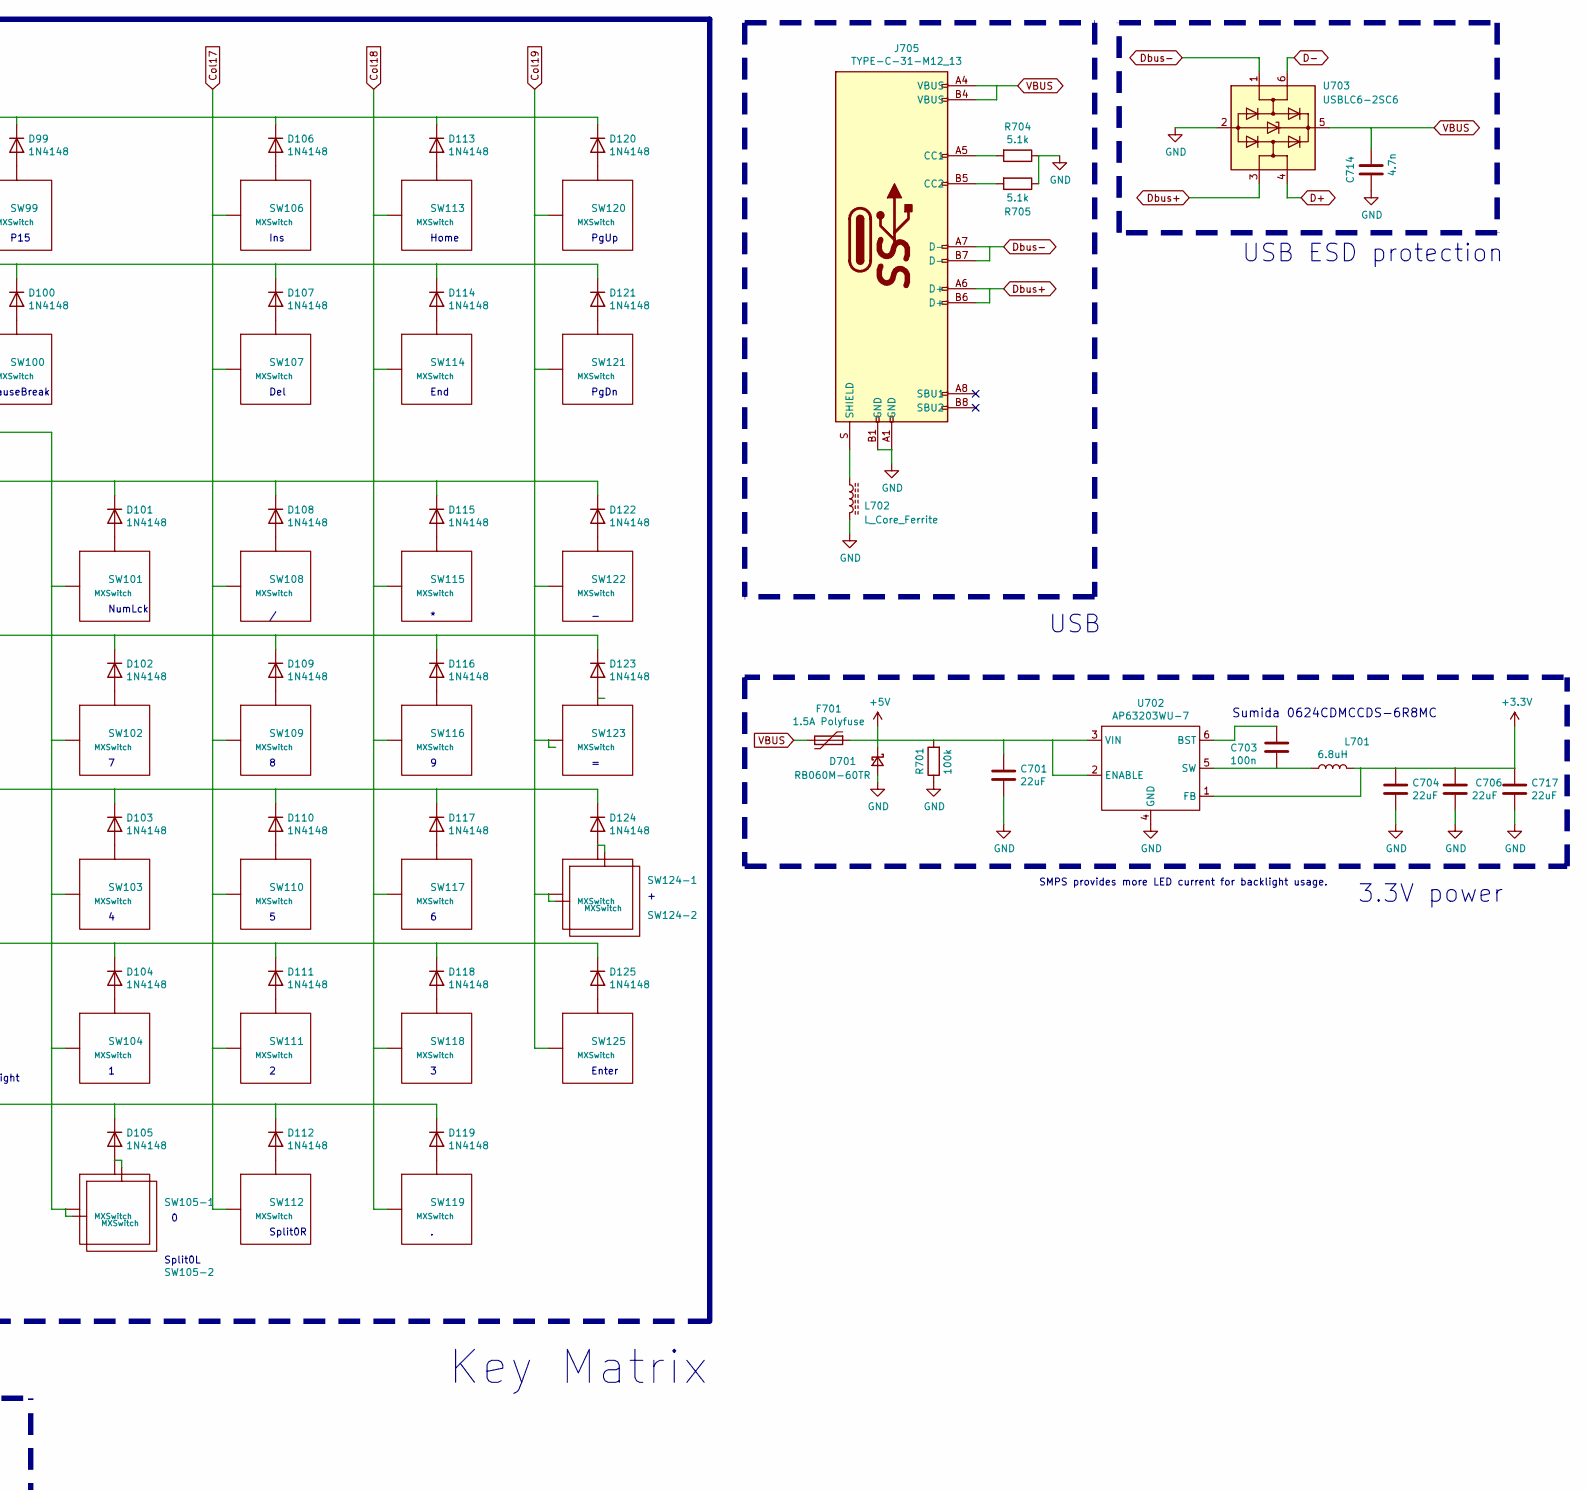
[picture p43: schematic Boston-keyboard-V06.kicad_sch, part in row 1, column 3]

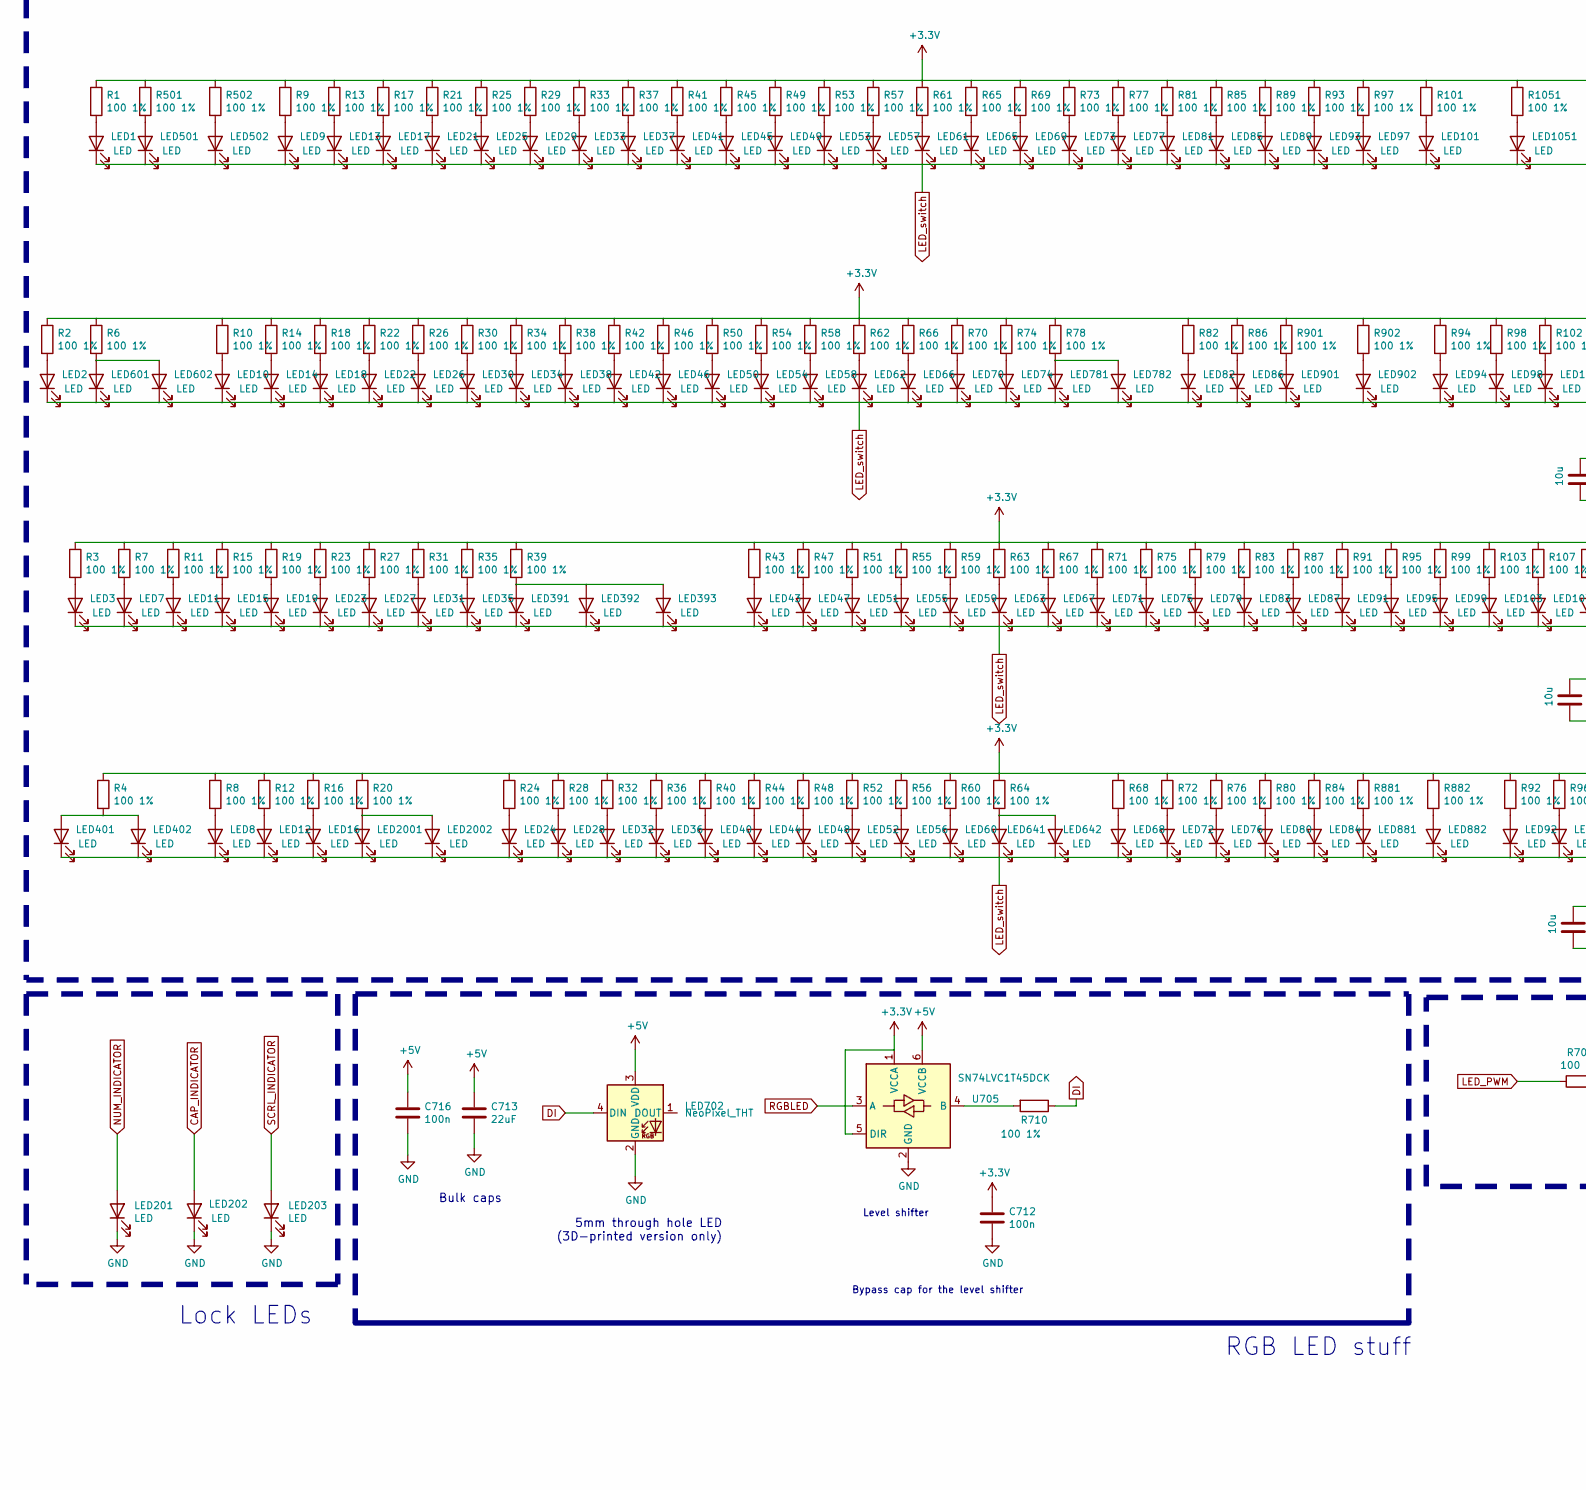
[picture p44: schematic Boston-keyboard-V06.kicad_sch, part in row 2, column 1]

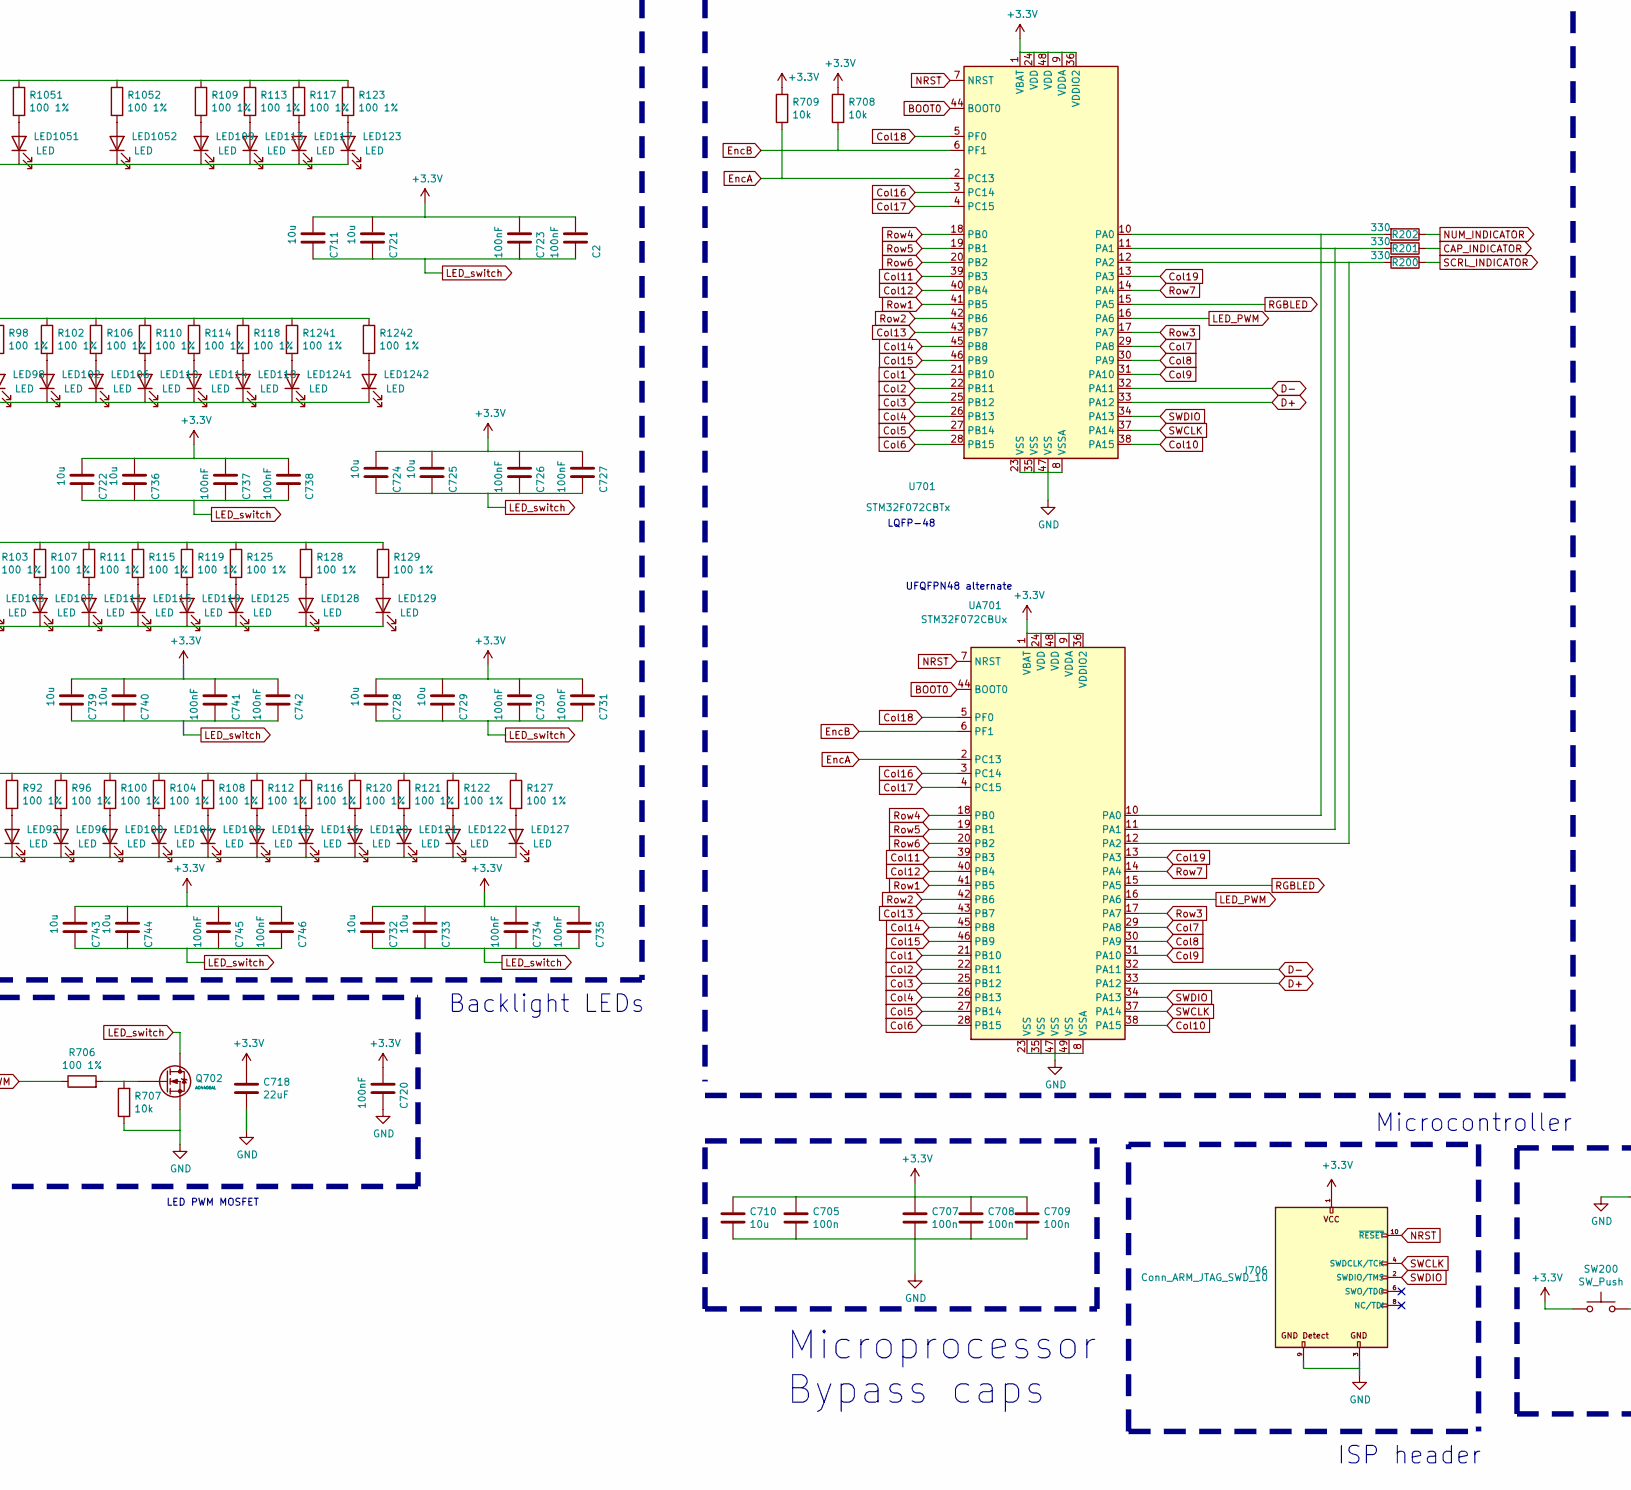
[picture p45: schematic Boston-keyboard-V06.kicad_sch, part in row 2, column 2]

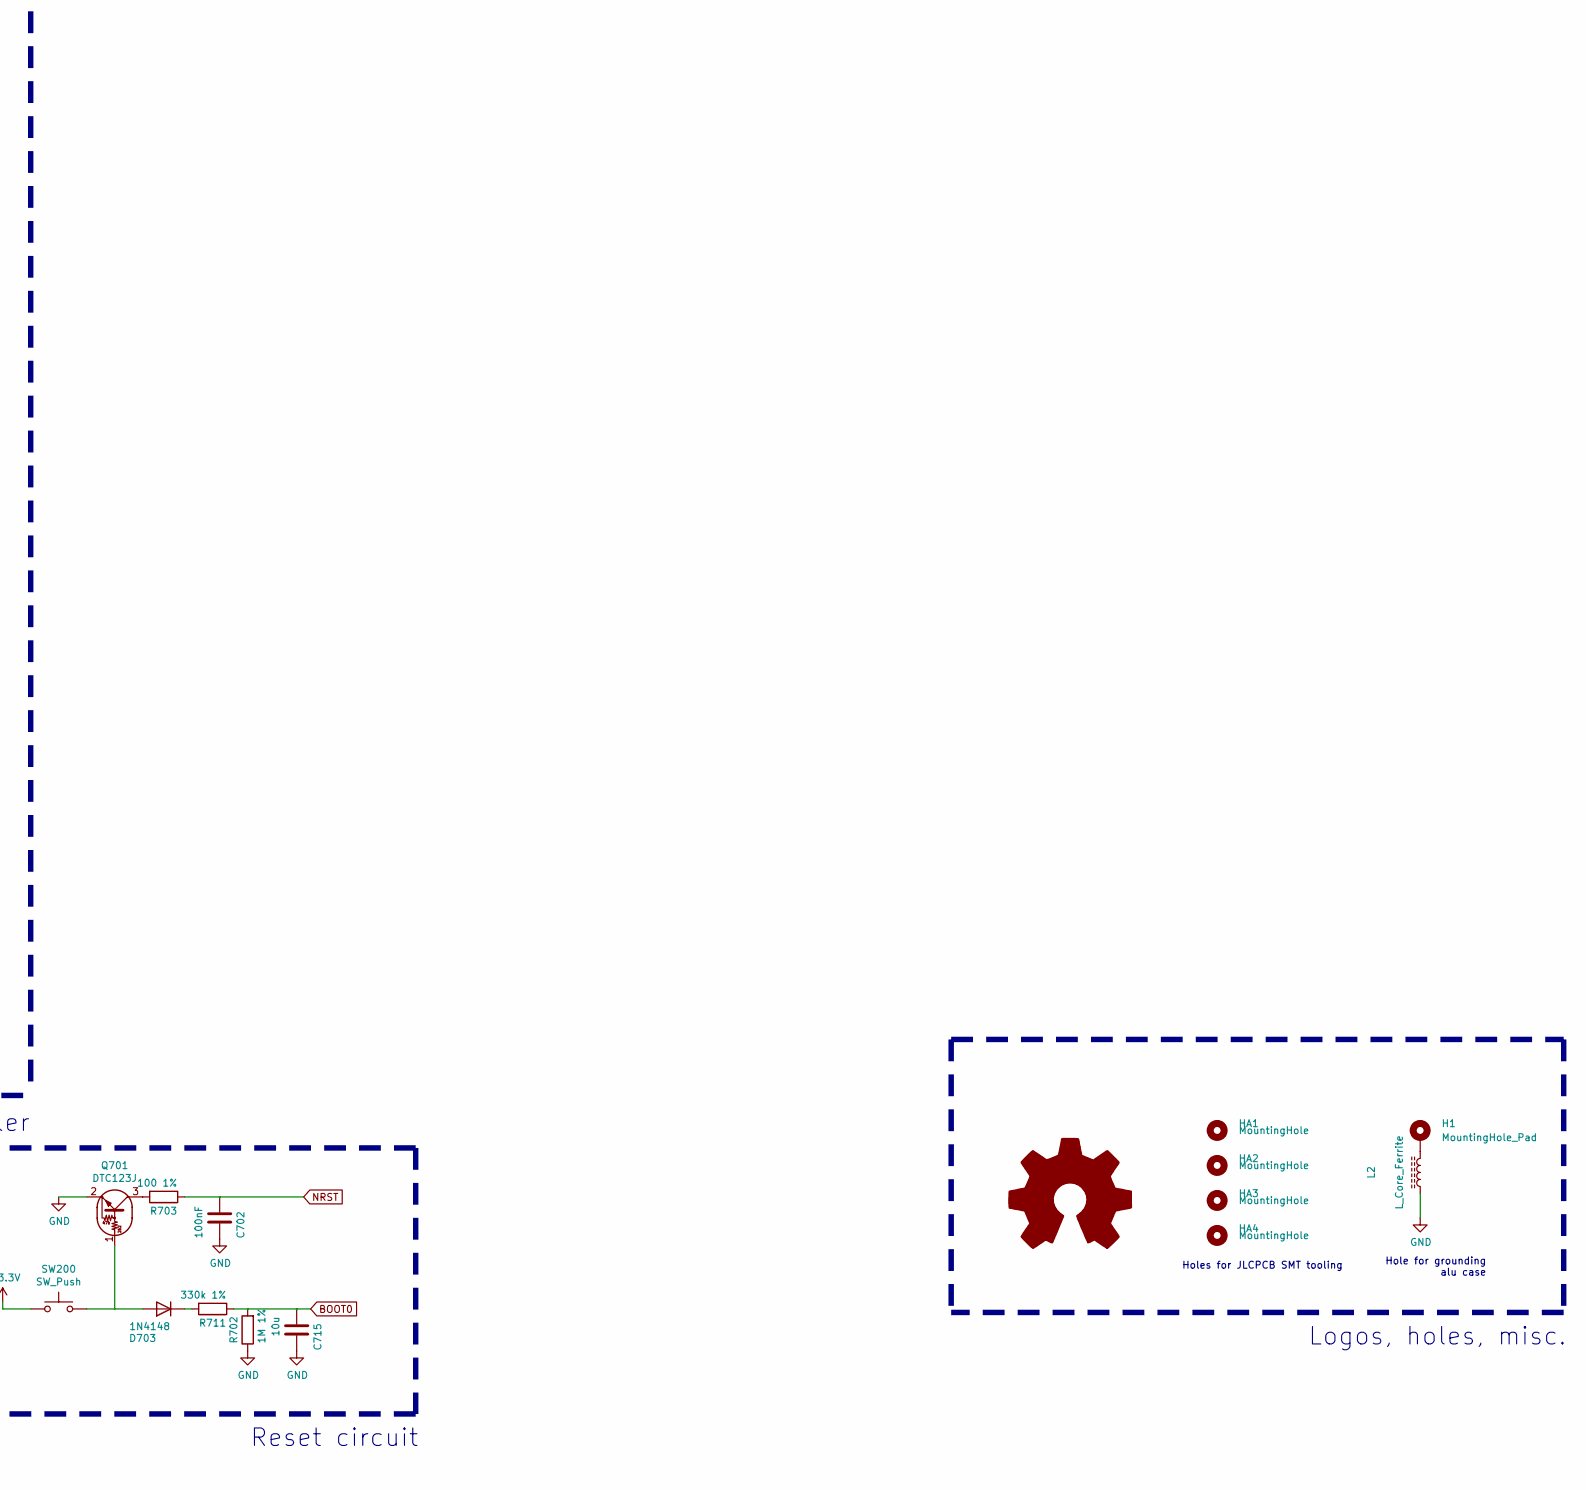
[picture p46: schematic Boston-keyboard-V06.kicad_sch, part in row 2, column 3]

Parts:
C2, C702, C720, C723, C726, C727, C730, C731, C734, C735, C737, C738, C741, C742, C745, C746: 100nF; C_0805_2012Metric_Pad1.15x1.40mm_HandSolder
C701, C704, C706, C713, C717, C718: 22uF; C_1206_3216Metric_Pad1.42x1.75mm_HandSolder
C703, C705, C707, C708, C709, C712, C716: 100n; C_0805_2012Metric_Pad1.15x1.40mm_HandSolder
C710, C711, C715, C721, C722, C724, C725, C728, C729, C732, C733, C736, C739, C740, C743, C744: 10u; C_1206_3216Metric_Pad1.42x1.75mm_HandSolder
C714: 4.7n; C_0805_2012Metric_Pad1.15x1.40mm_HandSolder
D1, D2, D3, D4, D5, D6, D7, D8, D9, D10, D11, D12, D13, D14, D15, D16, D17, D18, D19, D20, D21, D22, D23, D24, D25, D26, D27, D28, D29, D30, D31, D32, D33, D34, D35, D36, D37, D38, D39, D40, D41, D42, D43, D44, D45, D46, D47, D48, D49, D50, D51, D52, D53, D54, D55, D56, D57, D58, D59, D60, D61, D62, D63, D64, D65, D66, D67, D68, D69, D70, D71, D72, D73, D74, D75, D76, D77, D78, D79, D80, D81, D82, D83, D84, D85, D86, D87, D88, D89, D90, D91, D92, D93, D94, D95, D96, D97, D98, D99, D100, D101, D102, D103, D104, D105, D106, D107, D108, D109, D110, D111, D112, D113, D114, D115, D116, D117, D118, D119, D120, D121, D122, D123, D124, D125, D126, D127, D128, D129, D703: 1N4148; D_SOD-123
D701: RB060M-60TR; D_SOD-123
F701: 1.5A Polyfuse; Fuse_1812_4532Metric_Pad1.30x3.40mm_HandSolder
H1: MountingHole_Pad; MountingHole_3.5mm_Pad_Via
HA1, HA2, HA3, HA4: MountingHole; ToolingHole_1.152mm_(for_JLCPCB_SMT)
J705: TYPE-C-31-M12_13; TYPE-C-31-M-12
J706: Conn_ARM_JTAG_SWD_10; PinSocket_2x05_P2.54mm_Vertical
L1, L2, L702: L_Core_Ferrite; L_0805_2012Metric_Pad1.15x1.40mm_HandSolder
L701: 6.8uH; Sumida0624CDMCC
LED1, LED2, LED3, LED7, LED8, LED9, LED10, LED11, LED12, LED13, LED14, LED15, LED16, LED17, LED18, LED19, LED21, LED22, LED23, LED24, LED25, LED26, LED27, LED28, LED29, LED30, LED31, LED32, LED33, LED34, LED35, LED36, LED37, LED38, LED40, LED41, LED42, LED43, LED44, LED45, LED46, LED47, LED48, LED49, LED50, LED51, LED52, LED53, LED54, LED55, LED56, LED57, LED58, LED59, LED60, LED61, LED62, LED63, LED65, LED66, LED67, LED68, LED69, LED70, LED71, LED72, LED73, LED74, LED75, LED76, LED77, LED79, LED80, LED81, LED82, LED83, LED84, LED85, LED86, LED87, LED89, LED91, LED92, LED93, LED94, LED95, LED96, LED97, LED98, LED99, LED100, LED101, LED102, LED103, LED104, LED106, LED107, LED108, LED109, LED110, LED111, LED112, LED113, LED114, LED115, LED116, LED117, LED118, LED119, LED120, LED121, LED122, LED123, LED125, LED127, LED128, LED129, LED201, LED202, LED203, LED391, LED392, LED393, LED401, LED402, LED501, LED502, LED601, LED602, LED641, LED642, LED781, LED782, LED881, LED882, LED901, LED902, LED1051, LED1052, LED1241, LED1242, LED2001, LED2002: LED; LED_D3.0mm_Clear
LED702: NeoPixel_THT; LED_D5.0mm-4_RGB
LOGO2: Logo_Open_Hardware_Large; OSHW-Logo_11.4x12mm_SilkScreen
Q701: DTC123J; SOT-23
Q702: AO4406AL; SOIC-8
R1, R2, R3, R4, R6, R7, R8, R9, R10, R11, R12, R13, R14, R15, R16, R17, R18, R19, R20, R21, R22, R23, R24, R25, R26, R27, R28, R29, R30, R31, R32, R33, R34, R35, R36, R37, R38, R39, R40, R41, R42, R43, R44, R45, R46, R47, R48, R49, R50, R51, R52, R53, R54, R55, R56, R57, R58, R59, R60, R61, R62, R63, R64, R65, R66, R67, R68, R69, R70, R71, R72, R73, R74, R75, R76, R77, R78, R79, R80, R81, R82, R83, R84, R85, R86, R87, R89, R91, R92, R93, R94, R95, R96, R97, R98, R99, R100, R101, R102, R103, R104, R106, R107, R108, R109, R110, R111, R112, R113, R114, R115, R116, R117, R118, R119, R120, R121, R122, R123, R125, R127, R128, R129, R501, R502, R703, R706, R710, R881, R882, R901, R902, R1051, R1052, R1241, R1242: 100 1%; R_0805_2012Metric_Pad1.15x1.40mm_HandSolder
R200, R201, R202: 330; R_Axial_DIN0207_L6.3mm_D2.5mm_P7.62mm_Horizontal
R701: 100k; R_0805_2012Metric_Pad1.15x1.40mm_HandSolder
R702: 1M 1%; R_0805_2012Metric_Pad1.15x1.40mm_HandSolder
R704, R705: 5.1k; R_0805_2012Metric_Pad1.15x1.40mm_HandSolder
R707, R708, R709: 10k; R_0805_2012Metric_Pad1.15x1.40mm_HandSolder
R711: 330k 1%; R_0805_2012Metric_Pad1.15x1.40mm_HandSolder
SW1, SW2, SW7, SW8, SW9, SW10, SW11, SW12, SW14, SW15, SW16, SW17, SW18, SW19, SW21, SW22, SW23, SW24, SW25, SW26, SW27, SW28, SW29, SW30, SW31, SW32, SW33, SW34, SW35, SW36, SW37, SW38, SW40, SW41, SW42, SW43, SW44, SW45, SW46, SW47, SW48, SW49, SW50, SW51, SW52, SW53, SW54, SW55, SW56, SW57, SW58, SW59, SW60, SW61, SW62, SW63, SW64-1, SW65, SW66, SW67, SW68, SW69, SW70, SW71, SW72, SW73, SW74, SW75, SW76, SW77, SW78-1, SW79, SW80, SW81, SW82, SW83, SW85, SW86, SW87, SW88-1, SW91, SW92, SW93, SW94, SW95, SW96, SW97, SW98, SW99, SW100, SW101, SW102, SW103, SW104, SW105-2, SW106, SW107, SW108, SW109, SW110, SW111, SW112, SW113, SW114, SW115, SW116, SW117, SW118, SW119, SW120, SW121, SW122, SW123, SW124-2, SW127: MXSwitch; MX100
SW3, SW6-2, SW20-2, SW64-2, SW78-2, SW89: MXSwitch; MX150
SW4-1, SW5-1, SW6-1, SW13, SW20-1, SW39-3: MXSwitch; MX125
SW4-2, SW84: MXSwitch; MX175
SW5-2, SW90-1, SW128: MXSwitch; MX225
SW39-1: MXSwitch; MX625
SW39-2: MXSwitch; MX700
SW88-2, SW105-1, SW124-1: MXSwitch; MX200
SW90-2: MXSwitch; MX_ISOEnter
SW125: MXSwitch; MX200R
SW126: Rotary_Encoder_Switch_Chassis; ALPS_EC11E
SW129: MXSwitch; MX275
SW200: SW_Push; SW_PUSH_6mm_H5mm
U701: STM32F072CBTx; LQFP-48_7x7mm_P0.5mm
U702: AP63203WU-7; TSOT-23-6_HandSoldering
U703: USBLC6-2SC6; SOT-23-6
U705: SN74LVC1T45DCK; SOT-23-6_Handsoldering
UA701: STM32F072CBUx; QFN-48-1EP_7x7mm_P0.5mm_EP5.6x5.6mm

Connections:
+3.3V: C2.1, C704.1, C705.1, C706.1, C707.1, C708.1, C709.1, C710.1, C711.1, C712.1, C717.1, C718.1, C720.1, C721.1, C722.1, C723.1, C724.1, C725.1, C726.1, C727.1, C728.1, C729.1, C730.1, C731.1, C732.1, C733.1, C734.1, C735.1, C736.1, C737.1, C738.1, C739.1, C740.1, C741.1, C742.1, C743.1, C744.1, C745.1, C746.1, J706.1 (VCC), L701.2, R1.1, R2.1, R3.1, R4.1, R6.1, R7.1, R8.1, R9.1, R10.1, R11.1, R12.1, R13.1, R14.1, R15.1, R16.1, R17.1, R18.1, R19.1, R20.1, R21.1, R22.1, R23.1, R24.1, R25.1, R26.1, R27.1, R28.1, R29.1, R30.1, R31.1, R32.1, R33.1, R34.1, R35.1, R36.1, R37.1, R38.1, R39.1, R40.1, R41.1, R42.1, R43.1, R44.1, R45.1, R46.1, R47.1, R48.1, R49.1, R50.1, R51.1, R52.1, R53.1, R54.1, R55.1, R56.1, R57.1, R58.1, R59.1, R60.1, R61.1, R62.1, R63.1, R64.1, R65.1, R66.1, R67.1, R68.1, R69.1, R70.1, R71.1, R72.1, R73.1, R74.1, R75.1, R76.1, R77.1, R78.1, R79.1, R80.1, R81.1, R82.1, R83.1, R84.1, R85.1, R86.1, R87.1, R89.1, R91.1, R92.1, R93.1, R94.1, R95.1, R96.1, R97.1, R98.1, R99.1, R100.1, R101.1, R102.1, R103.1, R104.1, R106.1, R107.1, R108.1, R109.1, R110.1, R111.1, R112.1, R113.1, R114.1, R115.1, R116.1, R117.1, R118.1, R119.1, R120.1, R121.1, R122.1, R123.1, R125.1, R127.1, R128.1, R129.1, R501.1, R502.1, R708.2, R709.2, R881.1, R882.1, R901.1, R902.1, R1051.1, R1052.1, R1241.1, R1242.1, SW200.1, U701.1 (VBAT), U701.9 (VDDA), U701.24 (VDD), U701.36 (VDDIO2), U701.48 (VDD), U702.1 (FB), U705.1 (VCCA), U705.5 (DIR), UA701.1 (VBAT), UA701.9 (VDDA), UA701.24 (VDD), UA701.36 (VDDIO2), UA701.48 (VDD)
+5V: C701.1, C713.1, C716.1, D701.1 (K), F701.1, LED702.3 (VDD), R701.2, U702.2 (ENABLE), U702.3 (VIN), U705.6 (VCCB)
BOOT0: C715.1, R702.2, R711.1, U701.44 (BOOT0), UA701.44 (BOOT0)
CAP_INDICATOR: LED202.2 (A), R201.1
Col1: SW1.1 (Col), SW2.1 (Col), SW3.1 (Col), SW4-1.1 (Col), SW4-2.1 (Col), SW5-1.1 (Col), SW5-2.1 (Col), SW6-1.1 (Col), SW6-2.1 (Col), SW126.S1, U701.21 (PB10), UA701.21 (PB10)
Col2: SW7.1 (Col), SW8.1 (Col), SW9.1 (Col), SW10.1 (Col), SW11.1 (Col), SW12.1 (Col), SW13.1 (Col), U701.22 (PB11), UA701.22 (PB11)
Col3: SW14.1 (Col), SW15.1 (Col), SW16.1 (Col), SW17.1 (Col), SW18.1 (Col), SW19.1 (Col), SW20-1.1 (Col), SW20-2.1 (Col), U701.25 (PB12), UA701.25 (PB12)
Col4: SW21.1 (Col), SW22.1 (Col), SW23.1 (Col), SW24.1 (Col), SW25.1 (Col), SW26.1 (Col), U701.26 (PB13), UA701.26 (PB13)
Col5: SW27.1 (Col), SW28.1 (Col), SW29.1 (Col), SW30.1 (Col), SW31.1 (Col), SW32.1 (Col), SW128.1 (Col), U701.27 (PB14), UA701.27 (PB14)
Col6: SW33.1 (Col), SW34.1 (Col), SW35.1 (Col), SW36.1 (Col), SW37.1 (Col), SW38.1 (Col), SW39-1.1 (Col), SW39-2.1 (Col), SW39-3.1 (Col), U701.28 (PB15), UA701.28 (PB15)
Col7: SW40.1 (Col), SW41.1 (Col), SW42.1 (Col), SW43.1 (Col), SW44.1 (Col), SW45.1 (Col), U701.29 (PA8), UA701.29 (PA8)
Col8: SW46.1 (Col), SW47.1 (Col), SW48.1 (Col), SW49.1 (Col), SW50.1 (Col), SW51.1 (Col), SW129.1 (Col), U701.30 (PA9), UA701.30 (PA9)
Col9: SW52.1 (Col), SW53.1 (Col), SW54.1 (Col), SW55.1 (Col), SW56.1 (Col), SW57.1 (Col), U701.31 (PA10), UA701.31 (PA10)
Col10: SW58.1 (Col), SW59.1 (Col), SW60.1 (Col), SW61.1 (Col), SW62.1 (Col), SW63.1 (Col), SW64-1.1 (Col), SW64-2.1 (Col), U701.38 (PA15), UA701.38 (PA15)
Col11: SW65.1 (Col), SW66.1 (Col), SW67.1 (Col), SW68.1 (Col), SW69.1 (Col), SW70.1 (Col), SW71.1 (Col), U701.39 (PB3), UA701.39 (PB3)
Col12: SW72.1 (Col), SW73.1 (Col), SW74.1 (Col), SW75.1 (Col), SW76.1 (Col), SW77.1 (Col), SW78-1.1 (Col), SW78-2.1 (Col), U701.40 (PB4), UA701.40 (PB4)
Col13: SW79.1 (Col), SW80.1 (Col), SW81.1 (Col), SW82.1 (Col), SW83.1 (Col), SW84.1 (Col), SW85.1 (Col), U701.43 (PB7), UA701.43 (PB7)
Col14: SW86.1 (Col), SW87.1 (Col), SW88-1.1 (Col), SW88-2.1 (Col), SW89.1 (Col), SW90-1.1 (Col), SW90-2.1 (Col), SW91.1 (Col), SW92.1 (Col), U701.45 (PB8), UA701.45 (PB8)
Col15: SW93.1 (Col), SW94.1 (Col), SW95.1 (Col), SW96.1 (Col), SW97.1 (Col), SW98.1 (Col), SW127.1 (Col), U701.46 (PB9), UA701.46 (PB9)
Col16: SW99.1 (Col), SW100.1 (Col), SW101.1 (Col), SW102.1 (Col), SW103.1 (Col), SW104.1 (Col), SW105-1.1 (Col), SW105-2.1 (Col), U701.3 (PC14), UA701.3 (PC14)
Col17: SW106.1 (Col), SW107.1 (Col), SW108.1 (Col), SW109.1 (Col), SW110.1 (Col), SW111.1 (Col), SW112.1 (Col), U701.4 (PC15), UA701.4 (PC15)
Col18: SW113.1 (Col), SW114.1 (Col), SW115.1 (Col), SW116.1 (Col), SW117.1 (Col), SW118.1 (Col), SW119.1 (Col), U701.5 (PF0), UA701.5 (PF0)
Col19: SW120.1 (Col), SW121.1 (Col), SW122.1 (Col), SW123.1 (Col), SW124-1.1 (Col), SW124-2.1 (Col), SW125.1 (Col), U701.13 (PA3), UA701.13 (PA3)
D+: U701.33 (PA12), U703.4 (I/O2), UA701.33 (PA12)
D-: U701.32 (PA11), U703.6 (I/O1), UA701.32 (PA11)
DI: LED702.4 (DIN), R710.1
Dbus+: J705.A6 (D+), J705.B6 (D+), U703.3 (I/O2)
Dbus-: J705.A7 (D-), J705.B7 (D-), U703.1 (I/O1)
EncA: R709.1, SW126.A, U701.2 (PC13), UA701.2 (PC13)
EncB: R708.1, SW126.B, U701.6 (PF1), UA701.6 (PF1)
GND: C701.2, C702.2, C704.2, C705.2, C706.2, C707.2, C708.2, C709.2, C710.2, C712.2, C713.2, C714.2, C715.2, C716.2, C717.2, C718.2, C720.2, D701.2 (A), J705.A1 (GND), J705.B1 (GND), J706.3 (GND), J706.5 (GND), J706.9 (GNDDetect), L1.2, L2.1, L702.2, LED201.1 (K), LED202.1 (K), LED203.1 (K), LED702.2 (GND), Q701.2 (E), Q702.1, Q702.2, Q702.3, R701.1, R702.1, R704.1, R705.1, R707.1, SW126.C, U701.8 (VSSA), U701.23 (VSS), U701.35 (VSS), U701.47 (VSS), U702.4 (GND), U703.2 (GND), U705.2 (GND), UA701.8 (VSSA), UA701.23 (VSS), UA701.35 (VSS), UA701.47 (VSS), UA701.49 (VSS)
LED_PWM: R706.1, U701.16 (PA6), UA701.16 (PA6)
LED_switch: C2.2, C711.2, C721.2, C722.2, C723.2, C724.2, C725.2, C726.2, C727.2, C728.2, C729.2, C730.2, C731.2, C732.2, C733.2, C734.2, C735.2, C736.2, C737.2, C738.2, C739.2, C740.2, C741.2, C742.2, C743.2, C744.2, C745.2, C746.2, LED1.1 (K), LED2.1 (K), LED3.1 (K), LED7.1 (K), LED8.1 (K), LED9.1 (K), LED10.1 (K), LED11.1 (K), LED12.1 (K), LED13.1 (K), LED14.1 (K), LED15.1 (K), LED16.1 (K), LED17.1 (K), LED18.1 (K), LED19.1 (K), LED21.1 (K), LED22.1 (K), LED23.1 (K), LED24.1 (K), LED25.1 (K), LED26.1 (K), LED27.1 (K), LED28.1 (K), LED29.1 (K), LED30.1 (K), LED31.1 (K), LED32.1 (K), LED33.1 (K), LED34.1 (K), LED35.1 (K), LED36.1 (K), LED37.1 (K), LED38.1 (K), LED40.1 (K), LED41.1 (K), LED42.1 (K), LED43.1 (K), LED44.1 (K), LED45.1 (K), LED46.1 (K), LED47.1 (K), LED48.1 (K), LED49.1 (K), LED50.1 (K), LED51.1 (K), LED52.1 (K), LED53.1 (K), LED54.1 (K), LED55.1 (K), LED56.1 (K), LED57.1 (K), LED58.1 (K), LED59.1 (K), LED60.1 (K), LED61.1 (K), LED62.1 (K), LED63.1 (K), LED65.1 (K), LED66.1 (K), LED67.1 (K), LED68.1 (K), LED69.1 (K), LED70.1 (K), LED71.1 (K), LED72.1 (K), LED73.1 (K), LED74.1 (K), LED75.1 (K), LED76.1 (K), LED77.1 (K), LED79.1 (K), LED80.1 (K), LED81.1 (K), LED82.1 (K), LED83.1 (K), LED84.1 (K), LED85.1 (K), LED86.1 (K), LED87.1 (K), LED89.1 (K), LED91.1 (K), LED92.1 (K), LED93.1 (K), LED94.1 (K), LED95.1 (K), LED96.1 (K), LED97.1 (K), LED98.1 (K), LED99.1 (K), LED100.1 (K), LED101.1 (K), LED102.1 (K), LED103.1 (K), LED104.1 (K), LED106.1 (K), LED107.1 (K), LED108.1 (K), LED109.1 (K), LED110.1 (K), LED111.1 (K), LED112.1 (K), LED113.1 (K), LED114.1 (K), LED115.1 (K), LED116.1 (K), LED117.1 (K), LED118.1 (K), LED119.1 (K), LED120.1 (K), LED121.1 (K), LED122.1 (K), LED123.1 (K), LED125.1 (K), LED127.1 (K), LED128.1 (K), LED129.1 (K), LED391.1 (K), LED392.1 (K), LED393.1 (K), LED401.1 (K), LED402.1 (K), LED501.1 (K), LED502.1 (K), LED601.1 (K), LED602.1 (K), LED641.1 (K), LED642.1 (K), LED781.1 (K), LED782.1 (K), LED881.1 (K), LED882.1 (K), LED901.1 (K), LED902.1 (K), LED1051.1 (K), LED1052.1 (K), LED1241.1 (K), LED1242.1 (K), LED2001.1 (K), LED2002.1 (K), Q702.5 (D), Q702.6, Q702.7, Q702.8
NRST: C702.1, J706.10 (~RESET~), R703.1, U701.7 (NRST), UA701.7 (NRST)
NUM_INDICATOR: LED201.2 (A), R202.1
unnamed: C703.1, U702.6 (BST)
unnamed: C703.2, L701.1, U702.5 (SW)
unnamed: D1.2 (A), SW1.2 (Row)
unnamed: D2.2 (A), SW2.2 (Row)
unnamed: D3.2 (A), SW3.2 (Row)
unnamed: D4.2 (A), SW4-1.2 (Row), SW4-2.2 (Row)
unnamed: D5.2 (A), SW5-1.2 (Row), SW5-2.2 (Row)
unnamed: D6.2 (A), SW6-1.2 (Row), SW6-2.2 (Row)
unnamed: D7.2 (A), SW7.2 (Row)
unnamed: D8.2 (A), SW8.2 (Row)
unnamed: D9.2 (A), SW9.2 (Row)
unnamed: D10.2 (A), SW10.2 (Row)
unnamed: D11.2 (A), SW11.2 (Row)
unnamed: D12.2 (A), SW12.2 (Row)
unnamed: D13.2 (A), SW13.2 (Row)
unnamed: D14.2 (A), SW14.2 (Row)
unnamed: D15.2 (A), SW15.2 (Row)
unnamed: D16.2 (A), SW16.2 (Row)
unnamed: D17.2 (A), SW17.2 (Row)
unnamed: D18.2 (A), SW18.2 (Row)
unnamed: D19.2 (A), SW19.2 (Row)
unnamed: D20.2 (A), SW20-1.2 (Row), SW20-2.2 (Row)
unnamed: D21.2 (A), SW21.2 (Row)
unnamed: D22.2 (A), SW22.2 (Row)
unnamed: D23.2 (A), SW23.2 (Row)
unnamed: D24.2 (A), SW24.2 (Row)
unnamed: D25.2 (A), SW25.2 (Row)
unnamed: D26.2 (A), SW26.2 (Row)
unnamed: D27.2 (A), SW27.2 (Row)
unnamed: D28.2 (A), SW28.2 (Row)
unnamed: D29.2 (A), SW29.2 (Row)
unnamed: D30.2 (A), SW30.2 (Row)
unnamed: D31.2 (A), SW31.2 (Row)
unnamed: D32.2 (A), SW32.2 (Row)
unnamed: D33.2 (A), SW33.2 (Row)
unnamed: D34.2 (A), SW34.2 (Row)
unnamed: D35.2 (A), SW35.2 (Row)
unnamed: D36.2 (A), SW36.2 (Row)
unnamed: D37.2 (A), SW37.2 (Row)
unnamed: D38.2 (A), SW38.2 (Row)
unnamed: D39.2 (A), SW39-1.2 (Row), SW39-2.2 (Row), SW39-3.2 (Row)
unnamed: D40.2 (A), SW40.2 (Row)
unnamed: D41.2 (A), SW41.2 (Row)
unnamed: D42.2 (A), SW42.2 (Row)
unnamed: D43.2 (A), SW43.2 (Row)
unnamed: D44.2 (A), SW44.2 (Row)
unnamed: D45.2 (A), SW45.2 (Row)
unnamed: D46.2 (A), SW46.2 (Row)
unnamed: D47.2 (A), SW47.2 (Row)
unnamed: D48.2 (A), SW48.2 (Row)
unnamed: D49.2 (A), SW49.2 (Row)
unnamed: D50.2 (A), SW50.2 (Row)
unnamed: D51.2 (A), SW51.2 (Row)
unnamed: D52.2 (A), SW52.2 (Row)
unnamed: D53.2 (A), SW53.2 (Row)
unnamed: D54.2 (A), SW54.2 (Row)
unnamed: D55.2 (A), SW55.2 (Row)
unnamed: D56.2 (A), SW56.2 (Row)
unnamed: D57.2 (A), SW57.2 (Row)
unnamed: D58.2 (A), SW58.2 (Row)
unnamed: D59.2 (A), SW59.2 (Row)
unnamed: D60.2 (A), SW60.2 (Row)
unnamed: D61.2 (A), SW61.2 (Row)
unnamed: D62.2 (A), SW62.2 (Row)
unnamed: D63.2 (A), SW63.2 (Row)
unnamed: D64.2 (A), SW64-1.2 (Row), SW64-2.2 (Row)
unnamed: D65.2 (A), SW65.2 (Row)
unnamed: D66.2 (A), SW66.2 (Row)
unnamed: D67.2 (A), SW67.2 (Row)
unnamed: D68.2 (A), SW68.2 (Row)
unnamed: D69.2 (A), SW69.2 (Row)
unnamed: D70.2 (A), SW70.2 (Row)
unnamed: D71.2 (A), SW71.2 (Row)
unnamed: D72.2 (A), SW72.2 (Row)
unnamed: D73.2 (A), SW73.2 (Row)
unnamed: D74.2 (A), SW74.2 (Row)
unnamed: D75.2 (A), SW75.2 (Row)
unnamed: D76.2 (A), SW76.2 (Row)
unnamed: D77.2 (A), SW77.2 (Row)
unnamed: D78.2 (A), SW78-1.2 (Row), SW78-2.2 (Row)
unnamed: D79.2 (A), SW79.2 (Row)
unnamed: D80.2 (A), SW80.2 (Row)
unnamed: D81.2 (A), SW81.2 (Row)
unnamed: D82.2 (A), SW82.2 (Row)
unnamed: D83.2 (A), SW83.2 (Row)
unnamed: D84.2 (A), SW84.2 (Row)
unnamed: D85.2 (A), SW85.2 (Row)
unnamed: D86.2 (A), SW86.2 (Row)
unnamed: D87.2 (A), SW87.2 (Row)
unnamed: D88.2 (A), SW88-1.2 (Row), SW88-2.2 (Row)
unnamed: D89.2 (A), SW89.2 (Row)
unnamed: D90.2 (A), SW90-1.2 (Row), SW90-2.2 (Row)
unnamed: D91.2 (A), SW91.2 (Row)
unnamed: D92.2 (A), SW92.2 (Row)
unnamed: D93.2 (A), SW93.2 (Row)
unnamed: D94.2 (A), SW94.2 (Row)
unnamed: D95.2 (A), SW95.2 (Row)
unnamed: D96.2 (A), SW96.2 (Row)
unnamed: D97.2 (A), SW97.2 (Row)
unnamed: D98.2 (A), SW98.2 (Row)
unnamed: D99.2 (A), SW99.2 (Row)
unnamed: D100.2 (A), SW100.2 (Row)
unnamed: D101.2 (A), SW101.2 (Row)
unnamed: D102.2 (A), SW102.2 (Row)
unnamed: D103.2 (A), SW103.2 (Row)
unnamed: D104.2 (A), SW104.2 (Row)
unnamed: D105.2 (A), SW105-1.2 (Row), SW105-2.2 (Row)
unnamed: D106.2 (A), SW106.2 (Row)
unnamed: D107.2 (A), SW107.2 (Row)
unnamed: D108.2 (A), SW108.2 (Row)
unnamed: D109.2 (A), SW109.2 (Row)
unnamed: D110.2 (A), SW110.2 (Row)
unnamed: D111.2 (A), SW111.2 (Row)
unnamed: D112.2 (A), SW112.2 (Row)
unnamed: D113.2 (A), SW113.2 (Row)
unnamed: D114.2 (A), SW114.2 (Row)
unnamed: D115.2 (A), SW115.2 (Row)
unnamed: D116.2 (A), SW116.2 (Row)
unnamed: D117.2 (A), SW117.2 (Row)
unnamed: D118.2 (A), SW118.2 (Row)
unnamed: D119.2 (A), SW119.2 (Row)
unnamed: D120.2 (A), SW120.2 (Row)
unnamed: D121.2 (A), SW121.2 (Row)
unnamed: D122.2 (A), SW122.2 (Row)
unnamed: D123.2 (A), SW123.2 (Row)
unnamed: D124.2 (A), SW124-1.2 (Row), SW124-2.2 (Row)
unnamed: D125.2 (A), SW125.2 (Row)
unnamed: D126.2 (A), SW126.S2
unnamed: D127.2 (A), SW127.2 (Row)
unnamed: D128.2 (A), SW128.2 (Row)
unnamed: D129.2 (A), SW129.2 (Row)
unnamed: D703.1 (K), R711.2
unnamed: D703.2 (A), Q701.1 (B), SW200.2
unnamed: H1.1, L2.2
unnamed: J705.A5 (CC1), R704.2
unnamed: J705.B5 (CC2), R705.2
unnamed: J705.S (SHIELD), L702.1
unnamed: L1.1, SW126.S (Shield)
unnamed: LED1.2 (A), R1.2
unnamed: LED2.2 (A), R2.2
unnamed: LED3.2 (A), R3.2
unnamed: LED7.2 (A), R7.2
unnamed: LED8.2 (A), R8.2
unnamed: LED9.2 (A), R9.2
unnamed: LED10.2 (A), R10.2
unnamed: LED11.2 (A), R11.2
unnamed: LED12.2 (A), R12.2
unnamed: LED13.2 (A), R13.2
unnamed: LED14.2 (A), R14.2
unnamed: LED15.2 (A), R15.2
unnamed: LED16.2 (A), R16.2
unnamed: LED17.2 (A), R17.2
unnamed: LED18.2 (A), R18.2
unnamed: LED19.2 (A), R19.2
unnamed: LED21.2 (A), R21.2
unnamed: LED22.2 (A), R22.2
unnamed: LED23.2 (A), R23.2
unnamed: LED24.2 (A), R24.2
unnamed: LED25.2 (A), R25.2
unnamed: LED26.2 (A), R26.2
unnamed: LED27.2 (A), R27.2
unnamed: LED28.2 (A), R28.2
unnamed: LED29.2 (A), R29.2
unnamed: LED30.2 (A), R30.2
unnamed: LED31.2 (A), R31.2
unnamed: LED32.2 (A), R32.2
unnamed: LED33.2 (A), R33.2
unnamed: LED34.2 (A), R34.2
unnamed: LED35.2 (A), R35.2
unnamed: LED36.2 (A), R36.2
unnamed: LED37.2 (A), R37.2
unnamed: LED38.2 (A), R38.2
unnamed: LED40.2 (A), R40.2
unnamed: LED41.2 (A), R41.2
unnamed: LED42.2 (A), R42.2
unnamed: LED43.2 (A), R43.2
unnamed: LED44.2 (A), R44.2
unnamed: LED45.2 (A), R45.2
unnamed: LED46.2 (A), R46.2
unnamed: LED47.2 (A), R47.2
unnamed: LED48.2 (A), R48.2
unnamed: LED49.2 (A), R49.2
unnamed: LED50.2 (A), R50.2
unnamed: LED51.2 (A), R51.2
unnamed: LED52.2 (A), R52.2
unnamed: LED53.2 (A), R53.2
unnamed: LED54.2 (A), R54.2
unnamed: LED55.2 (A), R55.2
unnamed: LED56.2 (A), R56.2
unnamed: LED57.2 (A), R57.2
unnamed: LED58.2 (A), R58.2
unnamed: LED59.2 (A), R59.2
unnamed: LED60.2 (A), R60.2
unnamed: LED61.2 (A), R61.2
unnamed: LED62.2 (A), R62.2
unnamed: LED63.2 (A), R63.2
unnamed: LED65.2 (A), R65.2
unnamed: LED66.2 (A), R66.2
unnamed: LED67.2 (A), R67.2
unnamed: LED68.2 (A), R68.2
unnamed: LED69.2 (A), R69.2
unnamed: LED70.2 (A), R70.2
unnamed: LED71.2 (A), R71.2
unnamed: LED72.2 (A), R72.2
unnamed: LED73.2 (A), R73.2
unnamed: LED74.2 (A), R74.2
unnamed: LED75.2 (A), R75.2
unnamed: LED76.2 (A), R76.2
unnamed: LED77.2 (A), R77.2
unnamed: LED79.2 (A), R79.2
unnamed: LED80.2 (A), R80.2
unnamed: LED81.2 (A), R81.2
unnamed: LED82.2 (A), R82.2
unnamed: LED83.2 (A), R83.2
unnamed: LED84.2 (A), R84.2
unnamed: LED85.2 (A), R85.2
unnamed: LED86.2 (A), R86.2
unnamed: LED87.2 (A), R87.2
unnamed: LED89.2 (A), R89.2
unnamed: LED91.2 (A), R91.2
unnamed: LED92.2 (A), R92.2
unnamed: LED93.2 (A), R93.2
unnamed: LED94.2 (A), R94.2
unnamed: LED95.2 (A), R95.2
unnamed: LED96.2 (A), R96.2
unnamed: LED97.2 (A), R97.2
unnamed: LED98.2 (A), R98.2
unnamed: LED99.2 (A), R99.2
unnamed: LED100.2 (A), R100.2
unnamed: LED101.2 (A), R101.2
unnamed: LED102.2 (A), R102.2
unnamed: LED103.2 (A), R103.2
unnamed: LED104.2 (A), R104.2
unnamed: LED106.2 (A), R106.2
unnamed: LED107.2 (A), R107.2
unnamed: LED108.2 (A), R108.2
unnamed: LED109.2 (A), R109.2
unnamed: LED110.2 (A), R110.2
unnamed: LED111.2 (A), R111.2
unnamed: LED112.2 (A), R112.2
unnamed: LED113.2 (A), R113.2
unnamed: LED114.2 (A), R114.2
unnamed: LED115.2 (A), R115.2
unnamed: LED116.2 (A), R116.2
unnamed: LED117.2 (A), R117.2
unnamed: LED118.2 (A), R118.2
unnamed: LED119.2 (A), R119.2
unnamed: LED120.2 (A), R120.2
unnamed: LED121.2 (A), R121.2
unnamed: LED122.2 (A), R122.2
unnamed: LED123.2 (A), R123.2
unnamed: LED125.2 (A), R125.2
unnamed: LED127.2 (A), R127.2
unnamed: LED128.2 (A), R128.2
unnamed: LED129.2 (A), R129.2
unnamed: LED391.2 (A), LED392.2 (A), LED393.2 (A), R39.2
unnamed: LED401.2 (A), LED402.2 (A), R4.2
unnamed: LED501.2 (A), R501.2
unnamed: LED502.2 (A), R502.2
unnamed: LED601.2 (A), LED602.2 (A), R6.2
unnamed: LED641.2 (A), LED642.2 (A), R64.2
unnamed: LED781.2 (A), LED782.2 (A), R78.2
unnamed: LED881.2 (A), R881.2
unnamed: LED882.2 (A), R882.2
unnamed: LED901.2 (A), R901.2
unnamed: LED902.2 (A), R902.2
unnamed: LED1051.2 (A), R1051.2
unnamed: LED1052.2 (A), R1052.2
unnamed: LED1241.2 (A), R1241.2
unnamed: LED1242.2 (A), R1242.2
unnamed: LED2001.2 (A), LED2002.2 (A), R20.2
unnamed: Q701.3 (C), R703.2
unnamed: Q702.4 (G), R706.2, R707.2
unnamed: R200.2, U701.12 (PA2), UA701.12 (PA2)
unnamed: R201.2, U701.11 (PA1), UA701.11 (PA1)
unnamed: R202.2, U701.10 (PA0), UA701.10 (PA0)
unnamed: R710.2, U705.4 (B)
RGBLED: U701.15 (PA5), U705.3 (A), UA701.15 (PA5)
Row1: D7.1 (K), D14.1 (K), D21.1 (K), D27.1 (K), D33.1 (K), D40.1 (K), D46.1 (K), D52.1 (K), D58.1 (K), D65.1 (K), D72.1 (K), D79.1 (K), D86.1 (K), D93.1 (K), D99.1 (K), D106.1 (K), D113.1 (K), D120.1 (K), D126.1 (K), U701.41 (PB5), UA701.41 (PB5)
Row2: D1.1 (K), D8.1 (K), D15.1 (K), D22.1 (K), D28.1 (K), D34.1 (K), D41.1 (K), D47.1 (K), D53.1 (K), D59.1 (K), D66.1 (K), D73.1 (K), D80.1 (K), D87.1 (K), D94.1 (K), D100.1 (K), D107.1 (K), D114.1 (K), D121.1 (K), U701.42 (PB6), UA701.42 (PB6)
Row3: D2.1 (K), D9.1 (K), D16.1 (K), D23.1 (K), D29.1 (K), D35.1 (K), D42.1 (K), D48.1 (K), D54.1 (K), D60.1 (K), D67.1 (K), D74.1 (K), D81.1 (K), D88.1 (K), D95.1 (K), D101.1 (K), D108.1 (K), D115.1 (K), D122.1 (K), U701.17 (PA7), UA701.17 (PA7)
Row4: D3.1 (K), D10.1 (K), D17.1 (K), D24.1 (K), D30.1 (K), D36.1 (K), D43.1 (K), D49.1 (K), D55.1 (K), D61.1 (K), D68.1 (K), D75.1 (K), D82.1 (K), D89.1 (K), D96.1 (K), D102.1 (K), D109.1 (K), D116.1 (K), D123.1 (K), U701.18 (PB0), UA701.18 (PB0)
Row5: D4.1 (K), D11.1 (K), D18.1 (K), D25.1 (K), D31.1 (K), D37.1 (K), D44.1 (K), D50.1 (K), D56.1 (K), D62.1 (K), D69.1 (K), D76.1 (K), D83.1 (K), D90.1 (K), D97.1 (K), D103.1 (K), D110.1 (K), D117.1 (K), D124.1 (K), U701.19 (PB1), UA701.19 (PB1)
Row6: D5.1 (K), D12.1 (K), D19.1 (K), D26.1 (K), D32.1 (K), D38.1 (K), D45.1 (K), D51.1 (K), D57.1 (K), D63.1 (K), D70.1 (K), D77.1 (K), D84.1 (K), D91.1 (K), D104.1 (K), D111.1 (K), D118.1 (K), D125.1 (K), D127.1 (K), U701.20 (PB2), UA701.20 (PB2)
Row7: D6.1 (K), D13.1 (K), D20.1 (K), D39.1 (K), D64.1 (K), D71.1 (K), D78.1 (K), D85.1 (K), D92.1 (K), D98.1 (K), D105.1 (K), D112.1 (K), D119.1 (K), D128.1 (K), D129.1 (K), U701.14 (PA4), UA701.14 (PA4)
SCRL_INDICATOR: LED203.2 (A), R200.1
SWCLK: J706.4 (SWDCLK/TCK), U701.37 (PA14), UA701.37 (PA14)
SWDIO: J706.2 (SWDIO/TMS), U701.34 (PA13), UA701.34 (PA13)
VBUS: C714.1, F701.2, J705.A4 (VBUS), J705.B4 (VBUS), U703.5 (VBUS)

Notes on the sheet:
Esc
Tab
Stepped
CapsLock
ISO Lshift
ANSI Lshift
LCtrl (1.25u)
LCtrl (1.5u)
Lock LEDs
ISO \ |
LWin
Bulk caps
LAlt (1.25u)
LAlt (1.5u)
5mm through hole LED (3D-printed version only)
Level shifter
Bypass cap for the level shifter
Split Space Left
6.25u Space
7u Space
1.25u Split Space Mid
RGB LED stuff
Split Space Right
LED PWM MOSFET
, <
RAlt (1u)
RAlt (1.5u)
P10
F10
; :
. >
Menu
Backlight LEDs
P11
F11
- _
' "
/ ?
Microprocessor Bypass caps
RCtrl (1u)
RCtrl (1.5u)
LQFP-48
P12
ISO `~
F12
= +
RShift
Left
UFQFPN48 alternate
Down
BackSpace
SplitBackspace
PrtSc
P13
ANSI Enter
ISO Enter
Right
Scroll Lock
P14
P16
P17
P18
SplitBackSpaceRight
ISP header
PauseBreak
P15
Microcontroller
NumLck
Split0L
Ins
Del
Split0R
Reset circuit
Home
End
Key Matrix
PgUp
PgDn
Enter
SMPS provides more LED current for backlight usage.
USB
Holes for JLCPCB SMT tooling
Sumida 0624CDMCCDS-6R8MC
Hole for grounding alu case
USB ESD protection
3.3V power
Logos, holes, misc.
